MarkJelic/TEC-1G/TEC-Deck/SoundTalker/Readme.md

# SoundTalker Audio Card

- SN76489 Sound Geberator
- SP0256A-AL2 Speech Processor
- Mix in standard TEC-1 Bit-Banged sounds
- Using LM3900 Op Amp
- 4 Layer board 

This is the Schematic: TEC-Deck SoundTalker Schematic

The "GroundWalker" connector is for bit-banged sound connection from the motherboard. Input is from the left pin, and the final amplified output goes to the right pin which is connected to the mini speaker on the motherboard. Without this Sound Card installed, you would just have a jumper over these two pins so that the bit-banged sound goes direct to the speaker.

This is Beta 2, using a LM3900 for pre-amp/mixer and amplifier:
TEC-Deck SoundTalker LM3900

These are are the Back (in Green) and Front (in Red) copper layers.

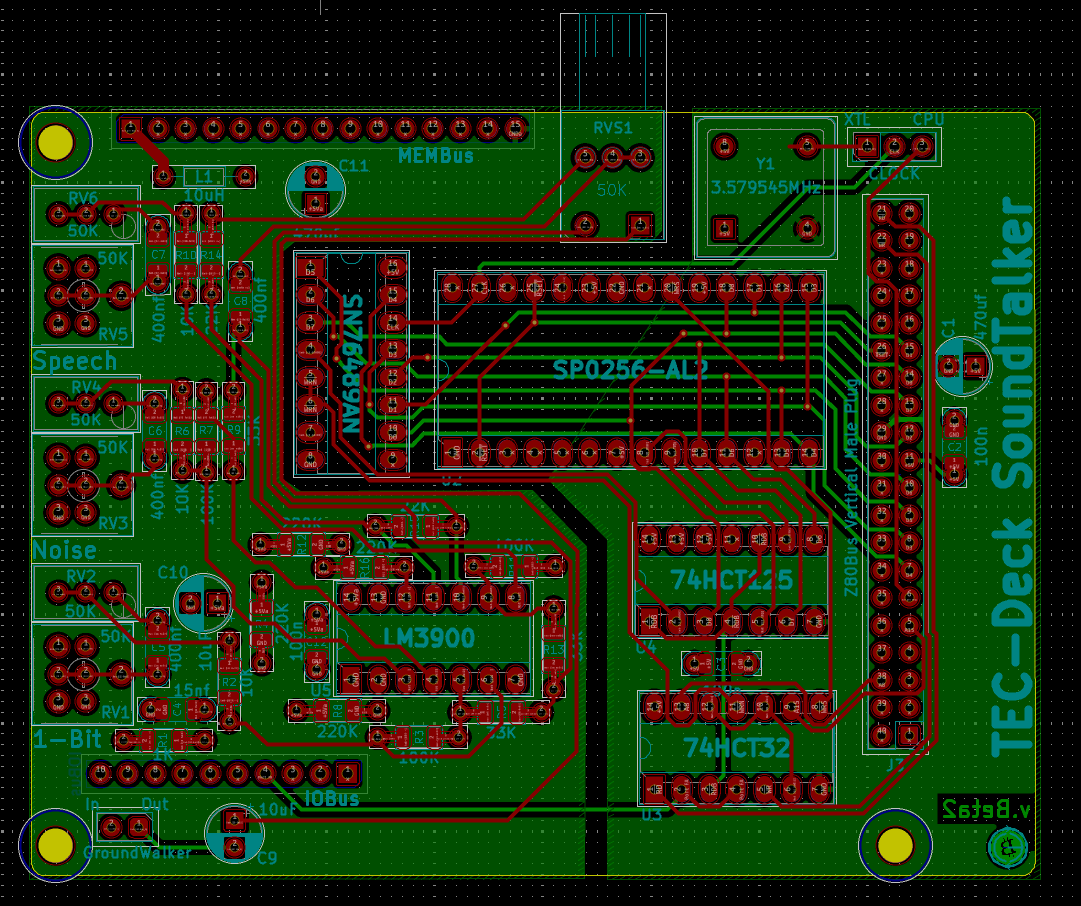
[picture p10: TEC-Deck/SoundTalker/SoundTalker-PCB_Back(G)+Front(R)_Layers.png]
TEC-Deck SoundTalker Back+Front


This is the second layer (the inner layer, closest to the back layer) and is used as the Ground plane. It also runs the source traces from each sound source, so that they are effectively shielded aby copper on all four sides.

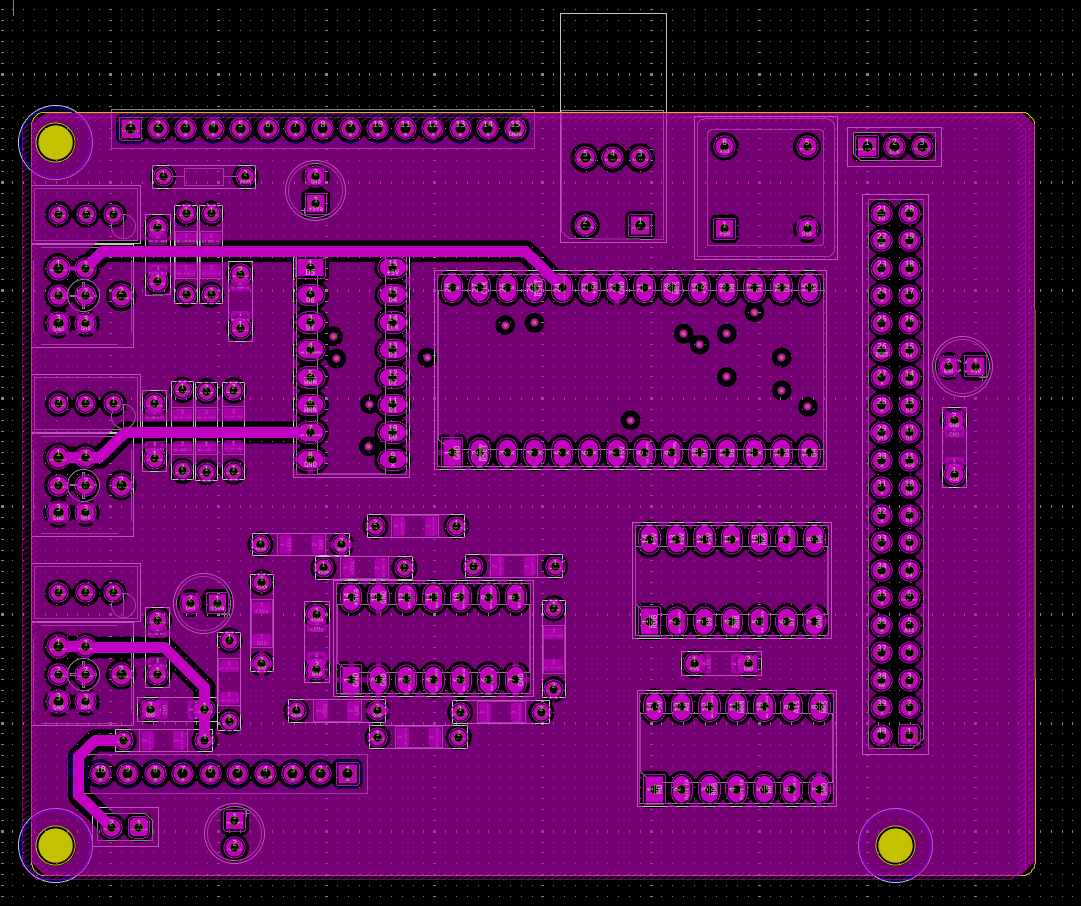
[picture p11: TEC-Deck/SoundTalker/SoundTalker-PCB_Layer2_GND-(Near_Back).png]
TEC-Deck SoundTalker Layer 2


The is the third layer (Inner layer, closer to the front of the board) and this runs the 5v plane. Note the split. Both are the same 5v source from the main motherboard, but the left hand (audio) side has an additional 10uH inductor to further smooth the 5v for the amplifier section.

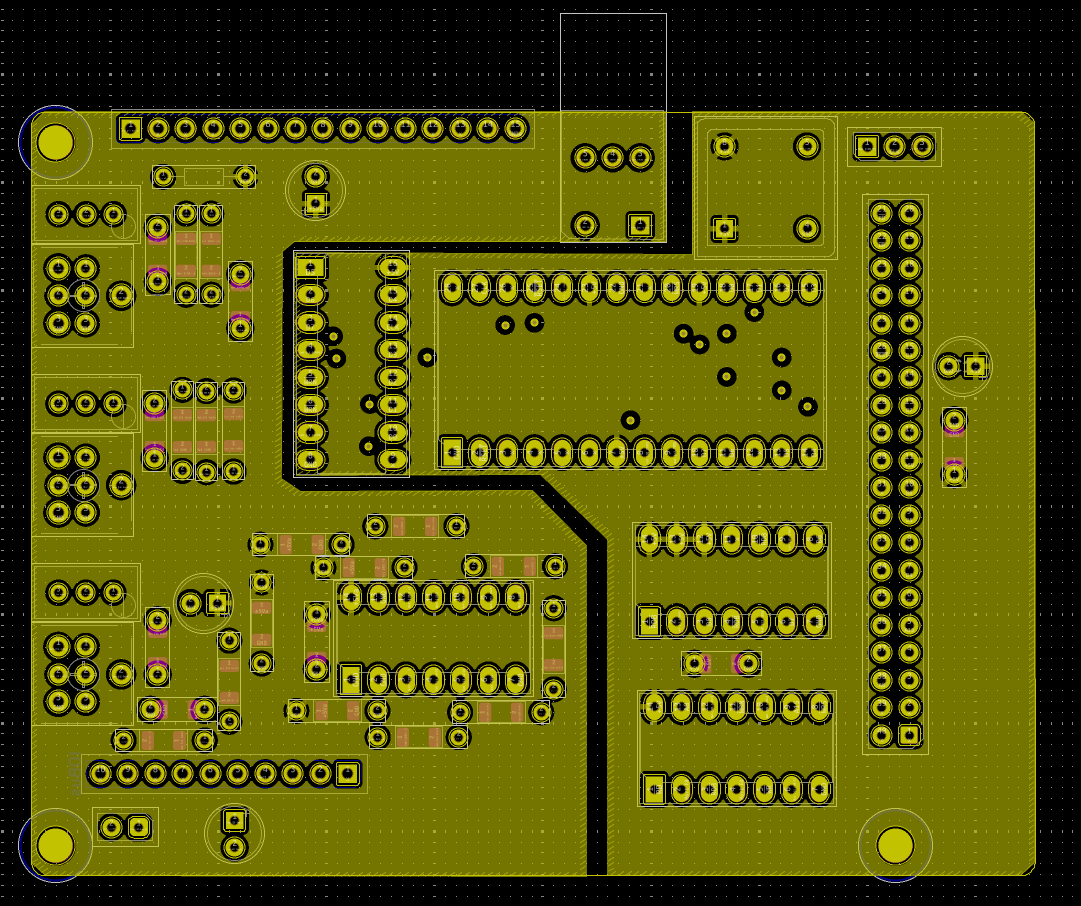
[picture p12: TEC-Deck/SoundTalker/SoundTalker-PCB_Layer3_5V-(Near_Front).png]
TEC-Deck SoundTalker Layer 3
