MarkJelic/TEC-1G/Z80Bus/TMS9918_Video-Card/README.md

# TMS9918 Video Card for the Z90Bus

All design files (KiCAD) and Gerbers.

Modelled after the 9918 video card design by J.B. Lang.
https://github.com/jblang/TMS9918A
