MarkJelic/TEC-1G/Cases/7Segs/Readme.md

## 3D Printed 7 segment display bezels for the TEC-1G
### by [Fred Nichols](https://github.com/turbo-gecko/TEC/tree/main/3D%20Printing/7%20Seg%20Bezel)

7Seg Bezel 3 Piece Lit
