MarkJelic/TEC-1G/TEC-Deck/Protoboard/Readme.md

# TEC-1G TEC-Deck Protoboard

Have an idea for the TEC-1G and want to quickly prototype it over the weekend?
Then you need one of these!

[Download the Gerbers](./TEC-1G_TEC-Deck_Protoboard_v1-0_Gerbers.zip) and get yourself a set so you're always ready for your creativity to flow.
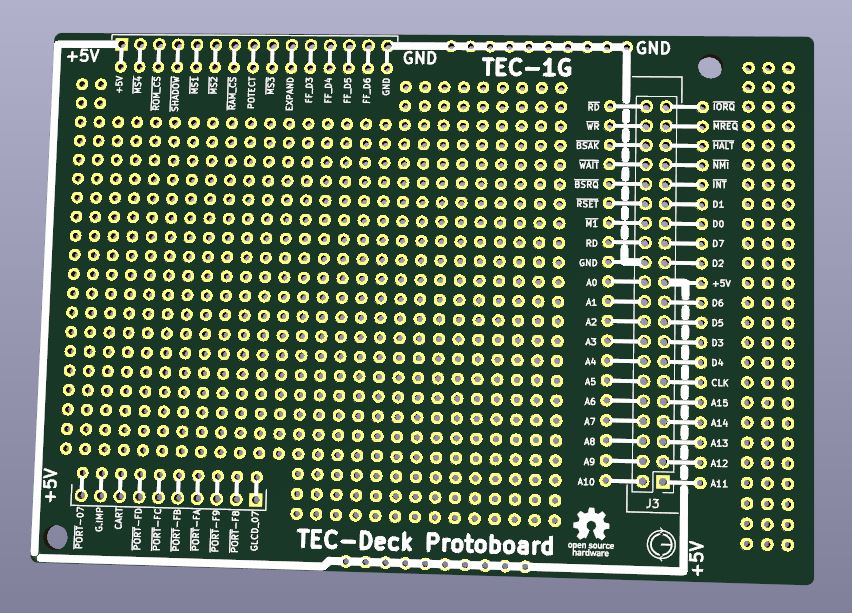
[picture p20: TEC-Deck/Protoboard/TEC-1G_TEC-Deck_ProtoBoard_v1_Render.JPG]
TEC-Deck Protoboard Render


Once you have designed your circuit and tested it out, why not make a PCB and share it with the TECian community!

[Download the KiCAD 7 design files](./TEC-1G_TEC-Deck_Protoboard_KiCAD-7.zip) of this board, and then removed the parts you don't need,
like all the through hole dots. Make sure you don't move the EdgeCuts, the Mounting Holes and of course the three headers
to ensure they line up with the TEC-1G motherboard.

If you wish to purchase a TEC-1G Proto-Pack which has this and any other Protoboards developed for the TEC-1G,
please check the listing on eBay:  https://www.ebay.com.au/itm/176243631024
