MarkJelic/TEC-1G/Cases/Retex/Readme.md

# The Original Retex Case for the TEC-1
A classic and still available after 40 years of production!

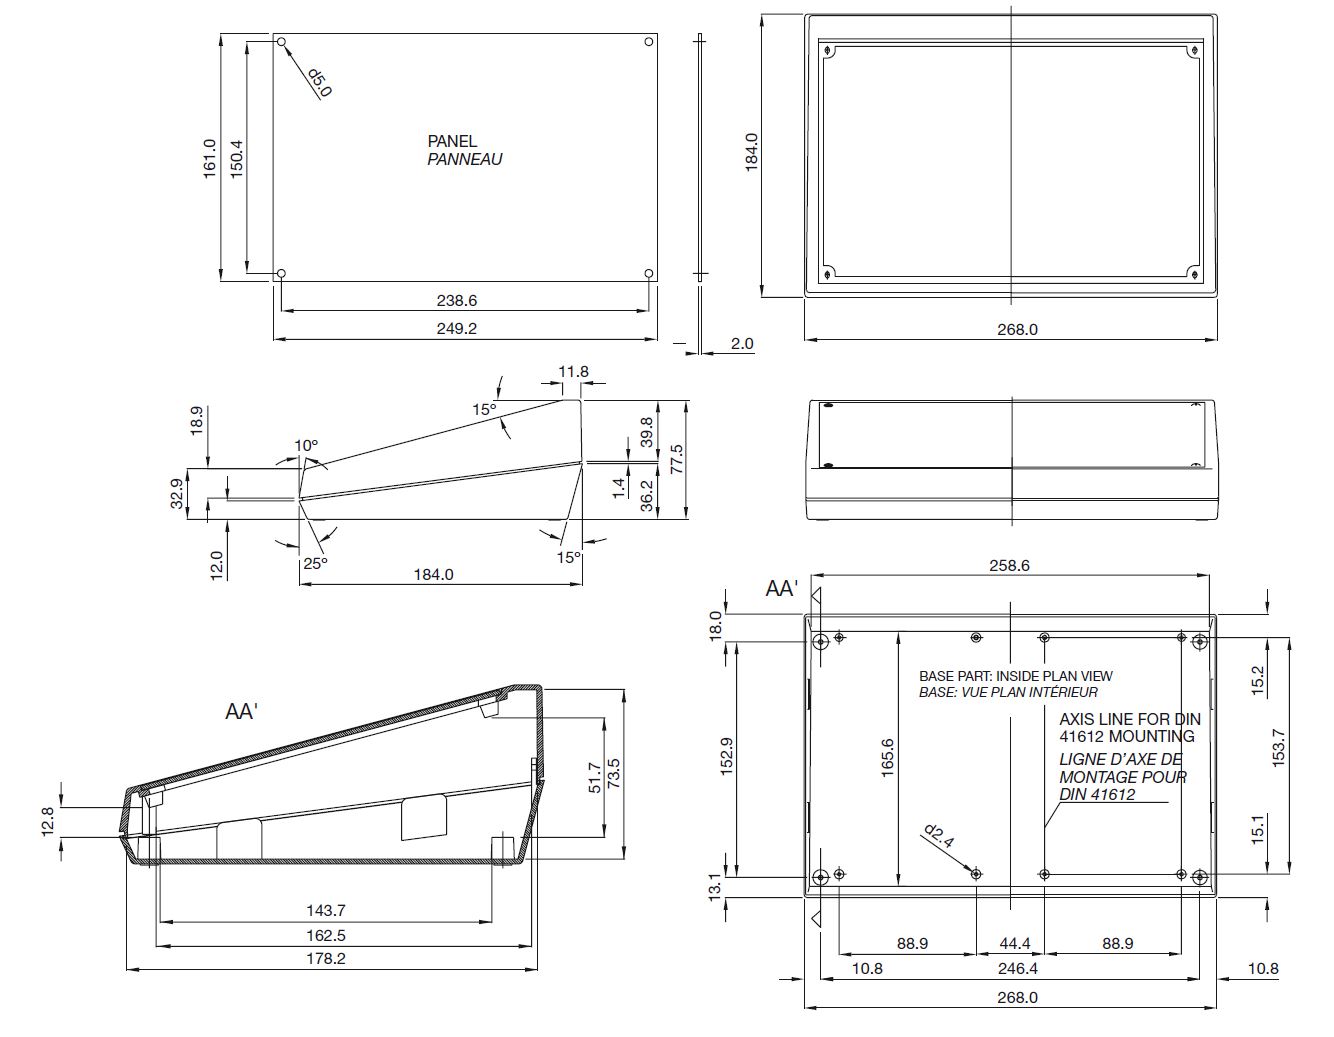
[picture p21: Cases/Retex/Retex_Case.jpg]
Retex
