MarkJelic/TEC-1G/Z80Bus/X4/Readme.md

# Z80Bus X4 System Board

Render

Here is a picture of the PCB that can be sourced from PCBWay or buy the entire kit off eBay.
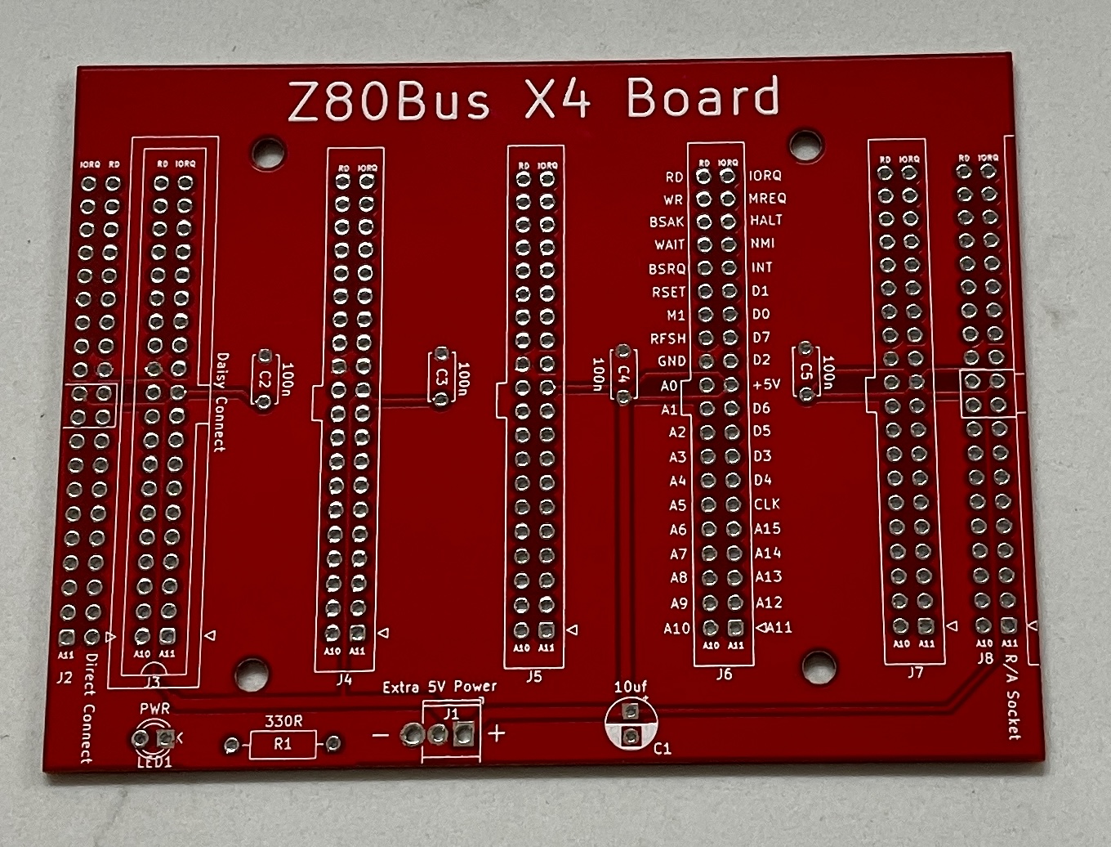
[picture p32: Z80Bus/X4/Z80Bus_X4_PCB.jpg]
PCB


Not there is much to gain from the schematic, but [here it is](Z80Bus_X4_Board_Schematic.pdf).
