MarkJelic/TEC-1G/Software/Games/8x8_LED/readme.md

# 8x8 LED Games & Demos

The original 8x8 was made with some clever soldering of 64 single colour LEDs.
Not many games were made for it but those that were, were greatly appreciated.
40 years later and the 8x8 has had a colour upgrade to full RGB which makes for
much more visually pleasing and distinguishable games and demos. 

The old mono games have been modified slightly for better keyboard layout 
and to allow hexpad / matrix keyboard input, or joystick input.
- All games default to Keyboard input.
- To activate Joystick input, hit Fn-J at the game's start menu.
- If you have the RTC card, and you turn on Joystick input, that selection will be remembered betwen games.
- To turn Keyboard input back on, hit Fn-K.

## Upcoming Titles
- Killer Tomatoes
- Maze Runner
- Minesweeper
- Scrambler
- King Tut's Snake
- RGB Invaders 3

## Pacmo  (John Hardy)

## Tecmo  (John Hardy)

## TEC Invaders 2  (Brian Chiha)

## Maze Treasure Hunt  (Brian Chiha)

## Maze  (Cameron Sheppard)

## TEC Invaders  (Cameron Sheppard)
