MarkJelic/TEC-1G/Z80Bus/TMS9918_Video-Card/KiCAD/README.md

## KiCAD Design Files

The design is NOT quite finished. I have 3 traces to complete. When this is done, will release Gerbers so people can print their own boards.

Note that I (think) I have hardwired the Port Address to be something in the range that the Colecovision and SG-1000 which gives us a HUGE library of games to port if anyone cares to.

NONE of this has been tested! You are on your own, but of course the community would love to see it come to life and be able to run some ported games! Keep us in the loop. Happy to work together.
