MarkJelic/TEC-1G/ROMs/MON3/readme.md

# Mon 3 User Guide

Mon3 (Talking Electronics Computer Monitor version 3) is custom-built for
the TEC-1G Single Board Z80 Computer. Mon3 is the heart of the TEC-1G. It
brings the hardware to life. Consider it an Operating System that provides
the ability to program the TEC. The monitor is jam-packed with features,
designed for beginners who are just learning to code Z80 and rich enough
for the advanced software developer.

A comprehensive User Guide has been provided that details how to use MON3.
Please download the **MON3 User Guide** linked in the File Links, below.

## File Links
| File | Description | Version |
|---|---|---|
| [MON3 for TEC-1G](./MON3-1G_BC25-16.bin) | Download and burn to a 16k ROM | 1.6 |
| [MON3 Change Log](./release_notes.md) | MON3 Change Log and Release Notes | 1.6 |
| [MON3 User Guide](./MON3_User_Guide_v1.6.pdf) | MON3 User Guide in PDF format | 1.6 |
| [MON3 API Guide](./api.md) | A summary of the APIs available in MON3 | 1.5 |

## A Brief Functional Description
The User Guide is a great resource that we recommend you print off and have at hand when writing
any programs for the TEC-1G.  Below are a few "Quick Reference" points that could also help.

###  Function Keys
Many of the function keys are just shortcuts to some of the Main Menu items,
like starting an Intel HEX Load. But others are really handy functions that can help
when programming "on the metal" of the TEC-1G. Here is a list of what the functions do.

Remember, to activate any of these, **Press and Hold the Fn Key down** while pressing on the corresponding function number.
Only release the Fn Key after the function starts. (There is a bit of a delay as to when the Cold Reset recognises you still pressing the Fn Key down, otherwise it just does a Warm Reset.)

| Key | Description | Implemented |
|---|---|---|
| Fn-RESET | Cold Boot the TEC-1G as if you just turned the Power On | 1.0 |
| Fn-AD (ESC) | Main Menu | 1.0 |
| Fn-GO (Enter) | Help Menu for Shortcut Fn- Keys | TBA |
| Fn-Minus (Left) | Delete current byte and SmartCopy™ RAM down | 1.0 |
| Fn-Plus (Right) | Insert a $00 byte and SmartCopy™ RAM up | 1.0 |
| Fn-0 | Configure QuickJump™ Locations | 1.3 |
| Fn-1 | QuickJump™ to Location 1 (Default is $4000. Stored in RTC) | 1.3 |
| Fn-2 | QuickJump™ to Location 2 (Stored in RTC) | 1.3 |
| Fn-3 | QuickJump™ to Location 3 (Stored in RTC) | 1.3 |
| Fn-4 | Initiate Intel HEX Load | 1.2 |
| Fn-5 | Toggle Terminal Output to GLCD. | 1.5 |
| Fn-6 | | TBA |
| Fn-7 | | TBA |
| Fn-8 | NOP Block Fill (Start, End, Value) | 1.5 |
| Fn-9 | | TBA |
| Fn-A | Restore Backup (Performs reverse of Fn-B) | 1.5 |
| Fn-B | Backup a block of memory from one location to another | 1.1 |
| Fn-C | SmartCopy™ a block of code from one location to another  | 1.0 |
| Fn-D | Disassembly View | 1.0 |
| Fn-E | Expand flag toggled (Bank 2, Pages 0 & 1)  | 1.1 |
| Fn-F | File Manager (SD Card) | 1.6 |

## Memory Map
One of the most clever things about the TEC-1G is the unique way it handles the limited 64K memory map
of the Zilog Z80.  The TEC-1G introduced 16Kb of ROM, yet was able to maintain backward compatibility with 2K ROMa,
that in the original TEC-1 was located right at the very bottom ($0000). If you want to find out more, head over to
[The Memory Map](https://github.com/MarkJelic/TEC-1G/blob/main/Documentation/memmap.md)
