MarkJelic/TEC-1G/Documentation/LCD_Cheat_Sheet.pdf

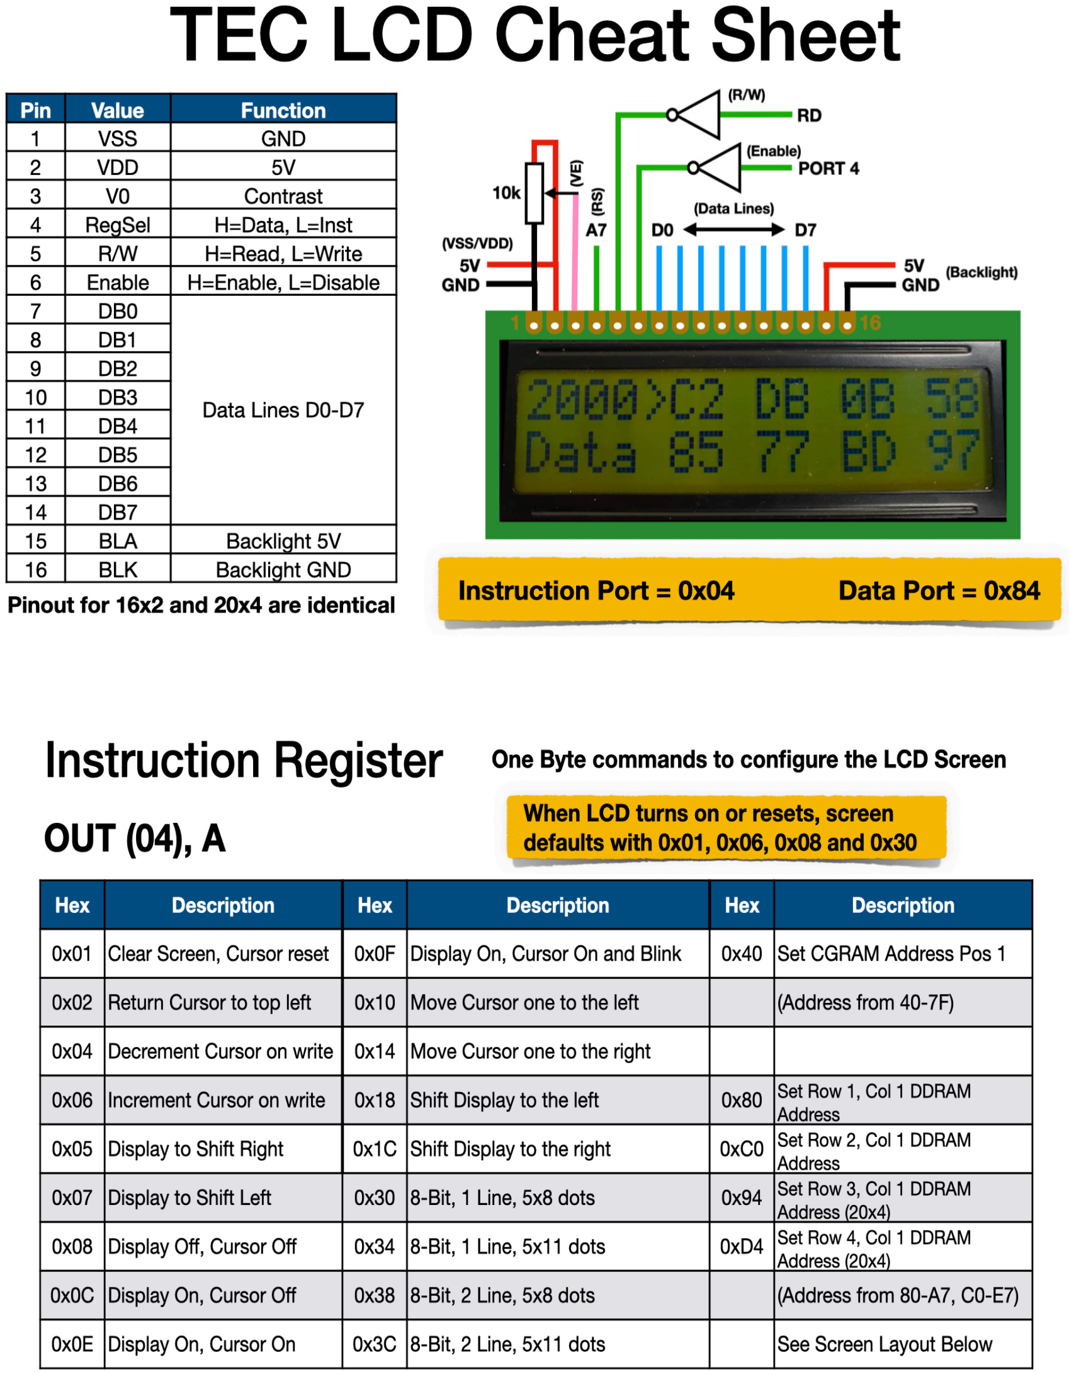
[picture p40: page 1]
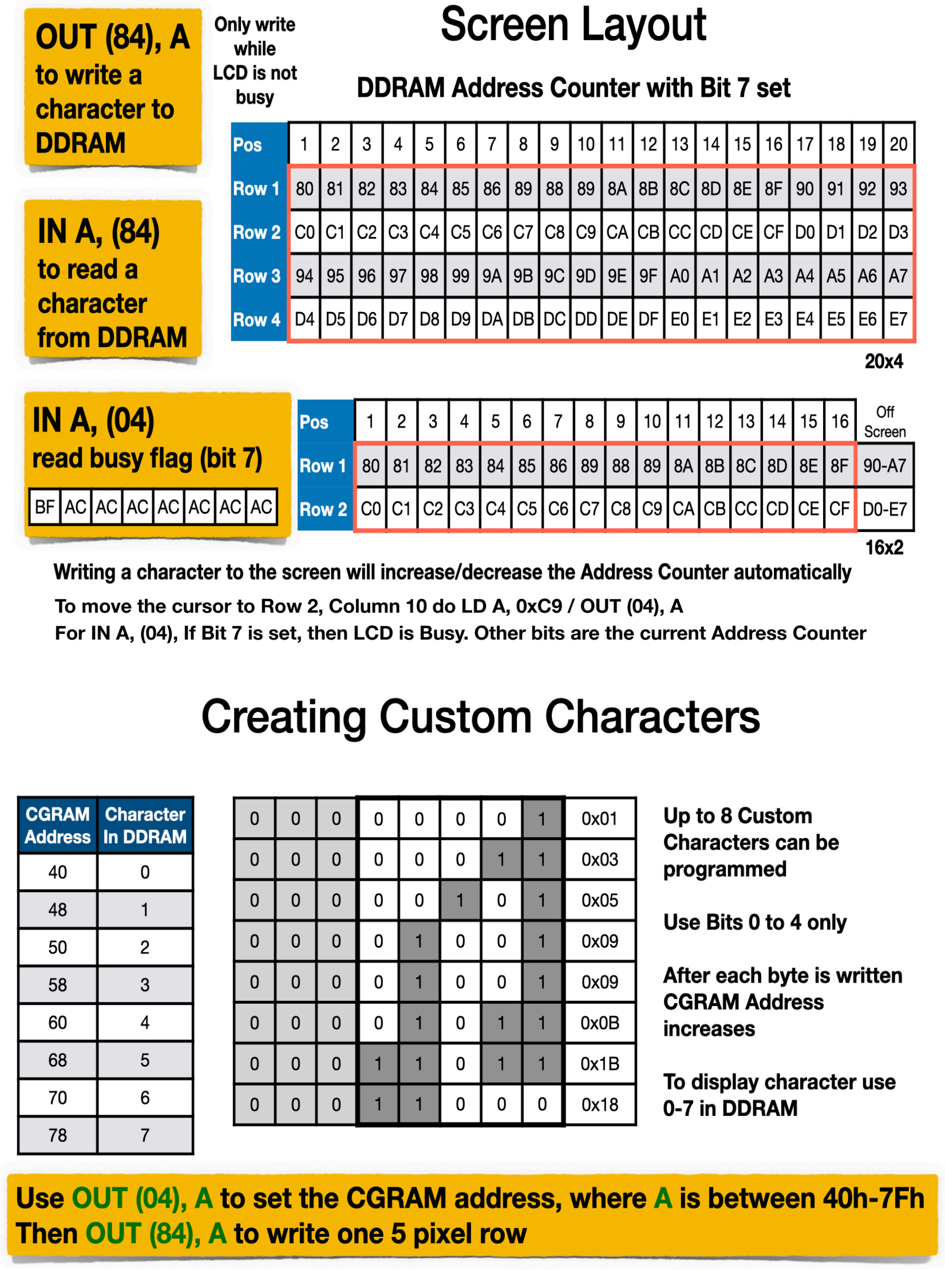
[picture p41: page 2]

## To move the cursor to Row 2, Column 10 do LD A, 0xC9 / OUT (04), A

For IN A, (04), If Bit 7 is set, then LCD is Busy. Other bits are the current Address Counter

# Character Table

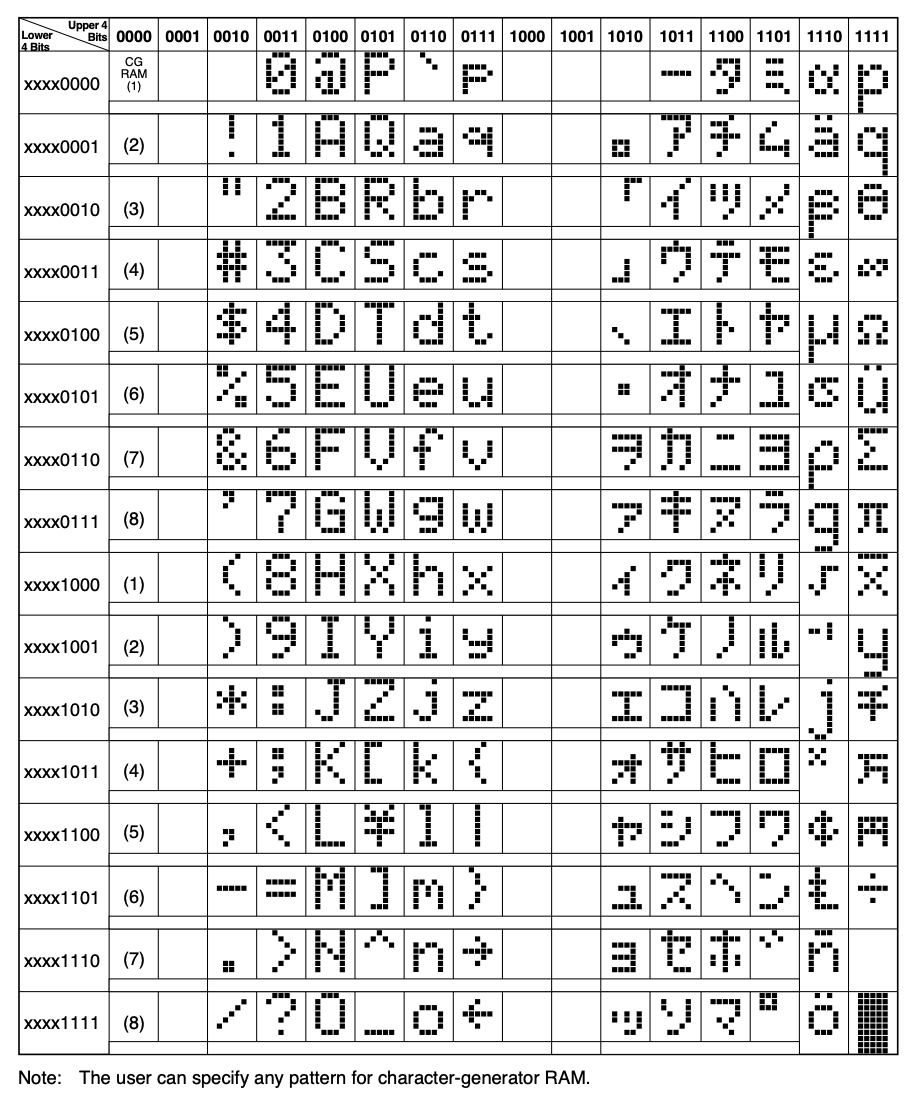
[picture p42: page 3]

# Example using CGRAM and DDRAM

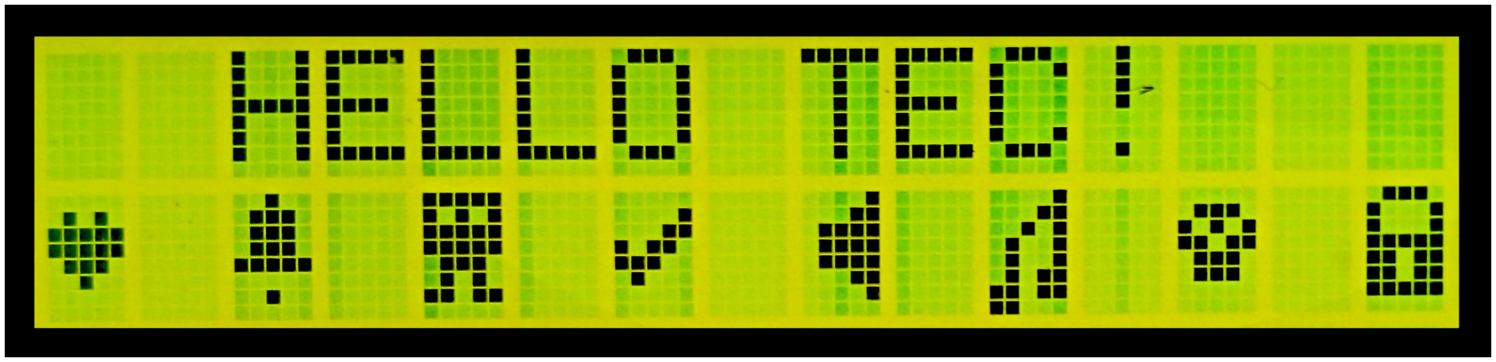
[picture p43: figure]

## Compiled by Brian Chiha v1.1

LCD_IR: | EQU | 04H ;Instruction Port
LCD_DR: | EQU | 84H ;Data Port

START:
; LCD set up
CALL | CHECK_BUSY | ;Check for LCD Busy
LD | A,0CH | ;Display On, Cursor Off
OUT | (LCD_IR),A | ;Send to Instruction Register (IR)
CALL | CHECK_BUSY | ;Check for LCD Busy
LD | A,38H | ;8-Bit, 2 Lines, 5x8 Characters
OUT | (LCD_IR),A | ;Send to Instruction Register (IR)

; Tell the LCD that next data will be to CGRAM
CALL | CHECK_BUSY | ;Check for LCD Busy
LD | A,40H | ;CGRAM entry
OUT | (LCD_IR),A | ;Send to Instruction Register (IR)

; Save multiple characters to CGRAM using lookup table and OUTI
LD | BC,4000H | LCD_DR | ;B=40 (8 letters), C=84 (port number)
LD | HL,TABLE | ;LCD custom character table
LOOP1:
CALL | CHECK_BUSY | ;Check for LCD Busy
OUTI | ;Send (HL) to port C, Decrement B, Increment HL
JR | NZ, LOOP1 | ;OUTI sets zero if B=0

; Display first line text
CALL | CHECK_BUSY | ;Check for LCD Busy
LD | A,82H | ;Move Cursor to Row 1, Col 3
OUT | (LCD_IR),A | ;Send to Instruction Register (IR)

; Send multiple characters using lookup table and OUTI
LD | BC,0A00H | LCD_DR | ;B=0A (10 letters), C=84 (port number)
LD | HL,TEXT | ;LCD text table
LOOP2:
CALL | CHECK_BUSY | ;Check for LCD Busy
OUTI | ;Send (HL) to port C, Decrement B, Increment HL
JR | NZ, LOOP2 | ;OUTI sets zero if B=0

; Display new characters
CALL | CHECK_BUSY | ;Check for LCD Busy
LD | A,0C0H | ;Move Cursor to Row 2, Col 1
OUT | (LCD_IR),A | ;Send to Instruction Register (IR)

; Send multiple characters using lookup table and OUTI
LD | BC,0800H | ;B=08 (letters), C=0 (CGRAM ref)
LOOP3:
CALL | CHECK_BUSY | ;Check for LCD Busy
LD | A,C | ;Send Custom Character
OUT | (LCD_DR),A | ;Send to Data Register (DR)
INC | C | ;Increase C to next CGRAM ref in DDRAM
CALL | CHECK_BUSY | ;Check for LCD Busy
LD | A,20H | ;Send Space Character
OUT | (LCD_DR),A | ;Send to Data Register (DR)
DJNZ | LOOP3 | ;Repeat for all 8 characters
HALT | ;Pause the CPU

TEXT:
DB "HELLO TEC!"
TABLE:
DB | 00H,0AH,1FH,1FH,0EH,04H,00H,00H | ;Heart
DB | 04H,0EH,0EH,0EH,1FH,00H,04H,00H | ;Bell
DB | 1FH,15H,1FH,1FH,0EH,0AH,1BH,00H | ;Alien
DB | 00H,01H,03H,16H,1CH,08H,00H,00H | ;Tick
DB | 01H,03H,0FH,0FH,0FH,03H,01H,00H | ;Speaker
DB | 01H,03H,05H,09H,09H,0BH,1BH,18H | ;Note
DB | 00H,0EH,15H,1BH,0EH,0EH,00H,00H | ;Skull
DB | 0EH,11H,11H,1FH,1BH,1BH,1FH,00H | ;Lock

; Routine to check the Busy Flag (Bit 7) CHECK_BUSY:
IN | A,(LCD_IR) | ;Read Busy Byte
RLCA | ;Put Bit 7 in Carry Flag
JR | C, CHECK_BUSY | ;If Carry Set then LCD is busy
RET
