MarkJelic/TEC-1G/Keyboards/Tactile/6mm_Tactile_Keyboard_Labels.pdf

R | AD | C | D | E | F
| GO | 8 | 9 | A | B
| - | 4 | 5 | 6 | 7
SH | + | 0 | 1 | 2 | 3
RESET | | | | | | | 22
| | | | | | | | | | | | | 1
AD Esc | ! 1 | @ 2 | # 3 | $ ₿ 4 | % 5 | ^ 6 | & 7 | * 8 | ( 9 | ) 0 | + = | BS
13
| TAB | Q | W | E | R | T | Y | U | I | O | P | _ - | | \
13
| CAPS | A | S | D F | G | H | J | K | L | : ; | " ' | GO Enter
13
| Shift | Z | X | C | V | B | N M | < , | > . | ? / | ↑ | Shift
13
| Ctrl | Fn | SPACE | - + ← | ↓ | →
6
| | | 59
White | 55 | Spare +1 | 60
