MarkJelic/TEC-1G/Cases/BrianC/TEC-1G Case.jpg

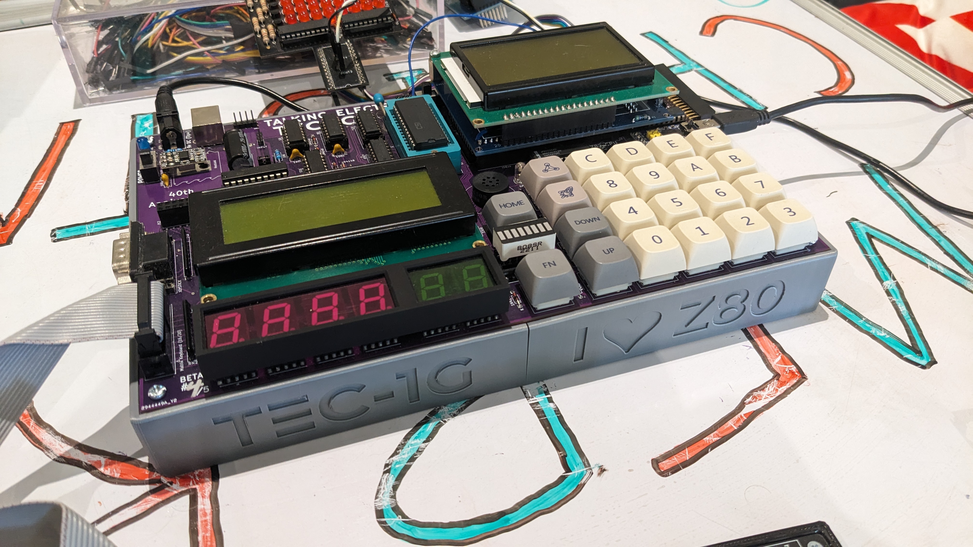
Cases/BrianC/TEC-1G Case.jpg
