MarkJelic/TEC-1G/Cases/Official/Tactile-Keyboard-Case_Purple-Front.jpg

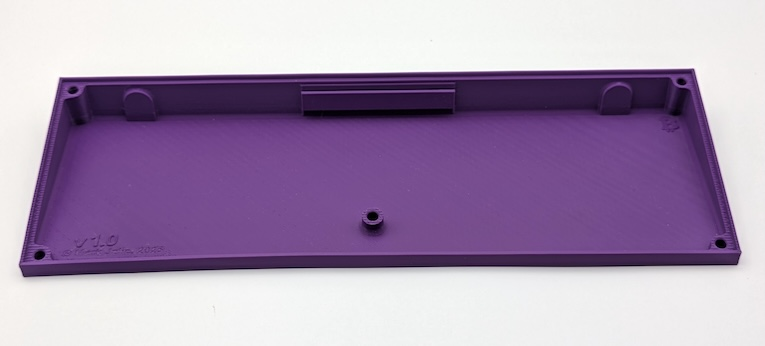
Cases/Official/Tactile-Keyboard-Case_Purple-Front.jpg
