MarkJelic/TEC-1G/Cases/Official/TEC-1G+Tactile-Keyboard_in_Cases_-_Left.jpg

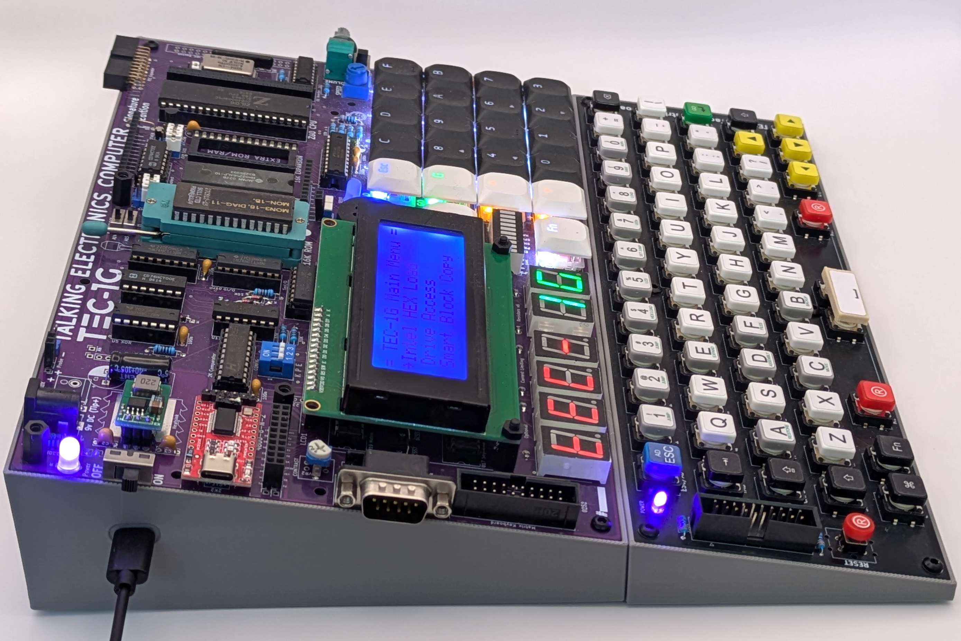
Cases/Official/TEC-1G+Tactile-Keyboard_in_Cases_-_Left.jpg
