MarkJelic/TEC-1G/Cases/Official/TEC-1G-in-Case_Back.jpg

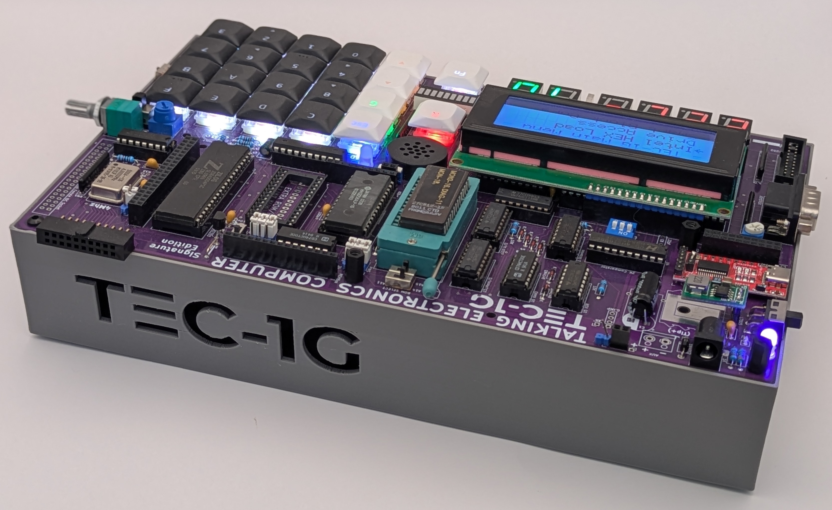
Cases/Official/TEC-1G-in-Case_Back.jpg
