MarkJelic/TEC-1G/Cases/Official/TEC-1G_Case_Tan+Grey.jpg

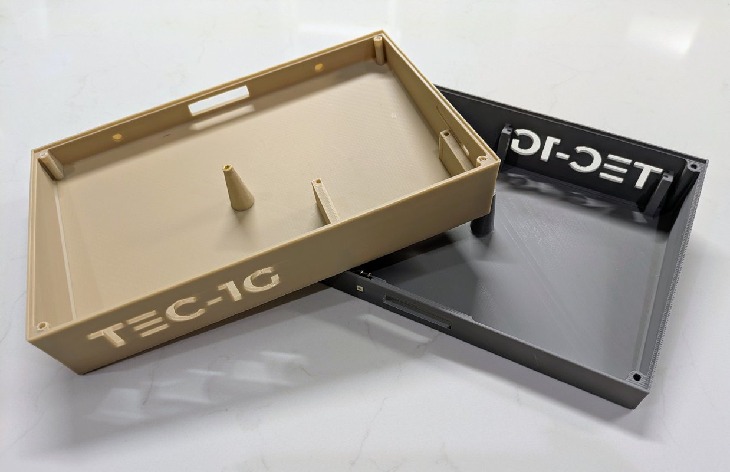
Cases/Official/TEC-1G_Case_Tan+Grey.jpg
