MarkJelic/TEC-1G/Keyboards/Mechanical/Mechncial_PCBs.jpg

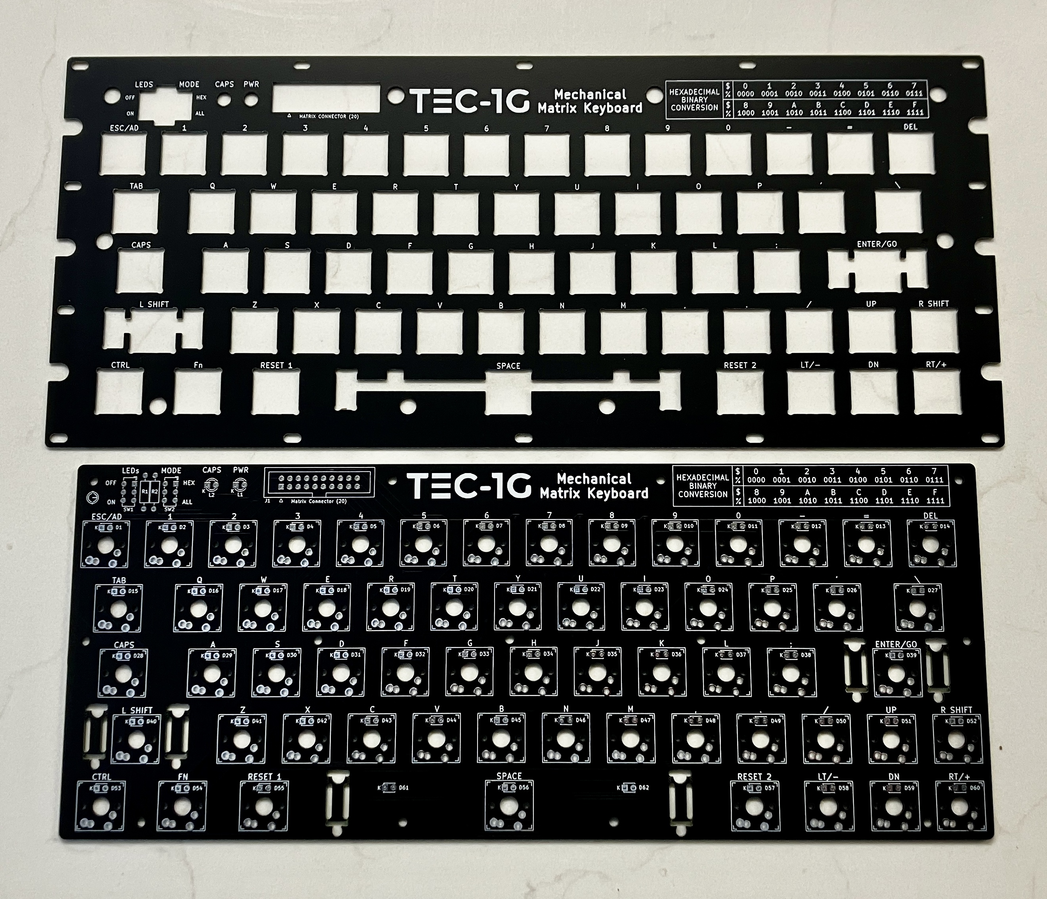
Keyboards/Mechanical/Mechncial_PCBs.jpg
