MarkJelic/TEC-1G/Keyboards/pictures/Scanning_Keyboard_Schematic1.jpg

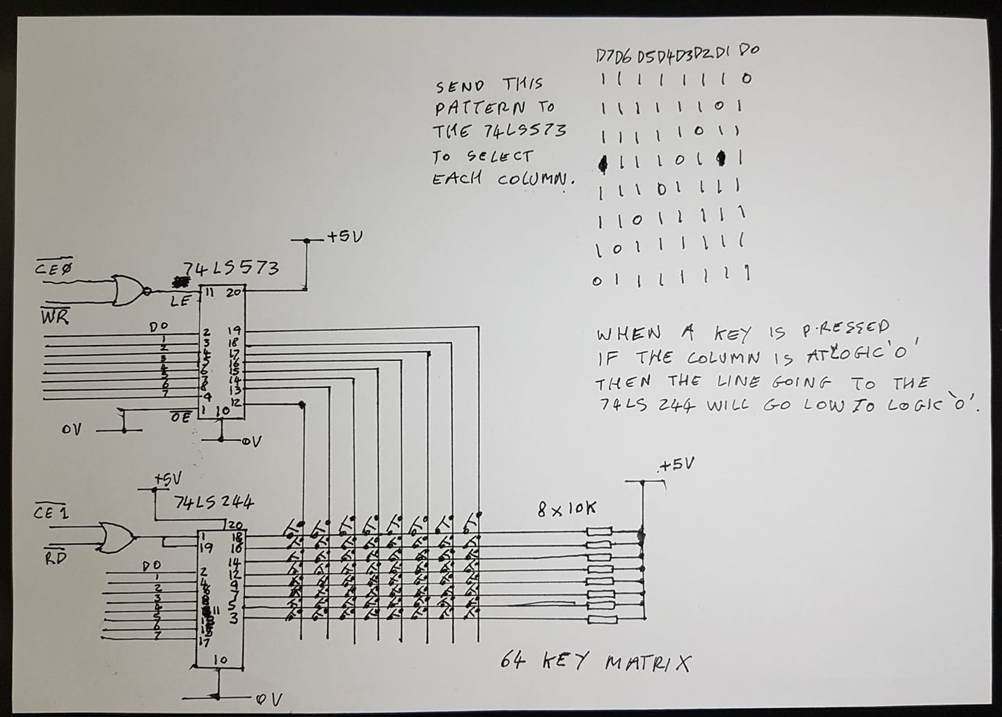
Keyboards/pictures/Scanning_Keyboard_Schematic1.jpg
