MarkJelic/TEC-1G/Keyboards/pictures/Scanning_Keyboard_Schematic2.jpg

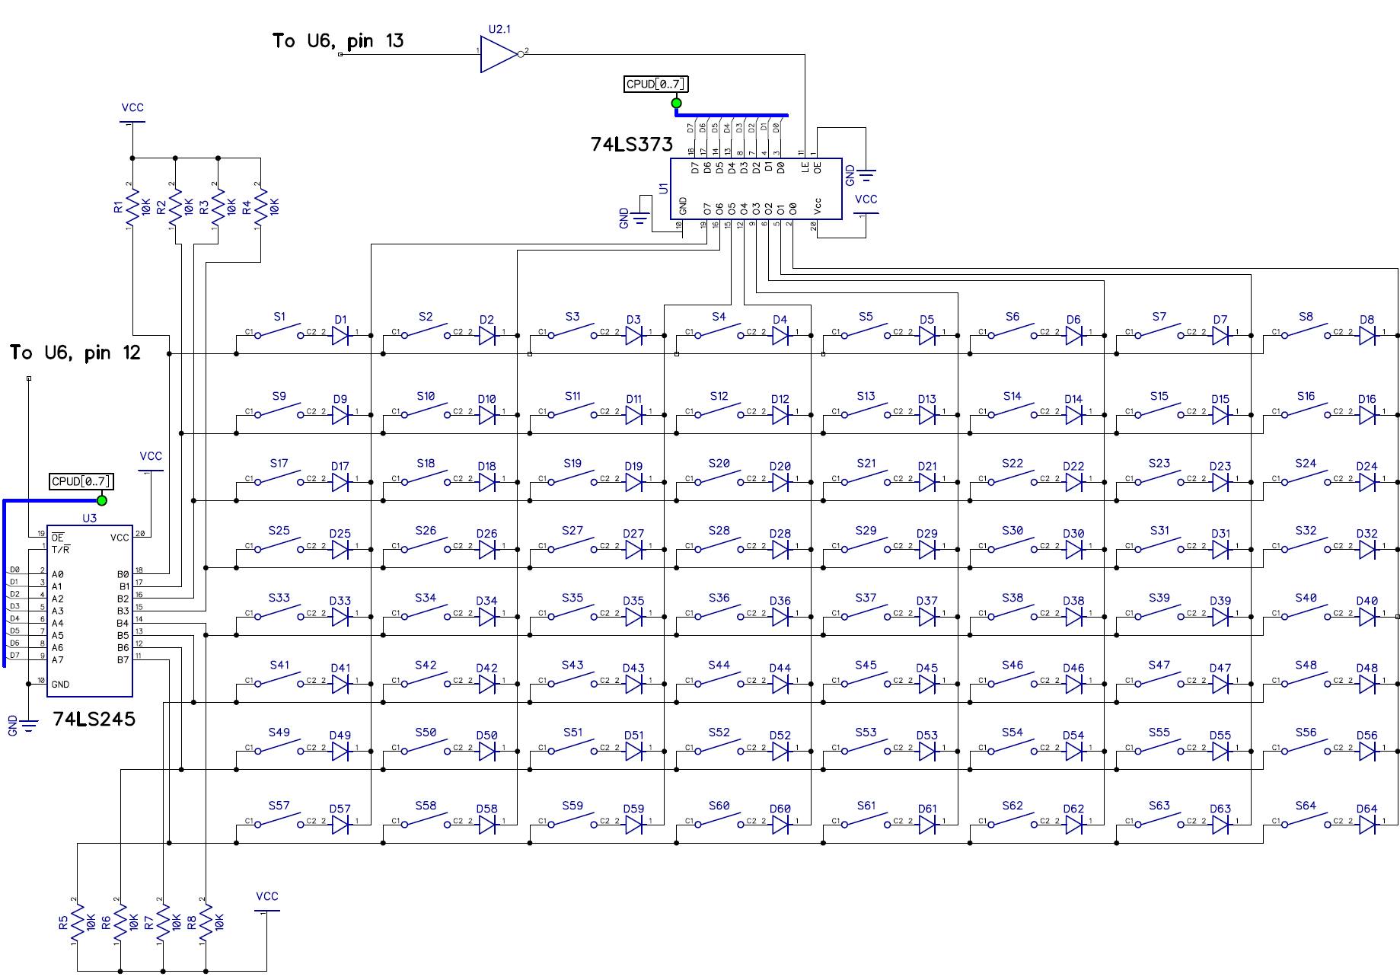
Keyboards/pictures/Scanning_Keyboard_Schematic2.jpg
