MarkJelic/TEC-1G/Keyboards/pictures/Spectrum_keyboard_for_Satellite.png

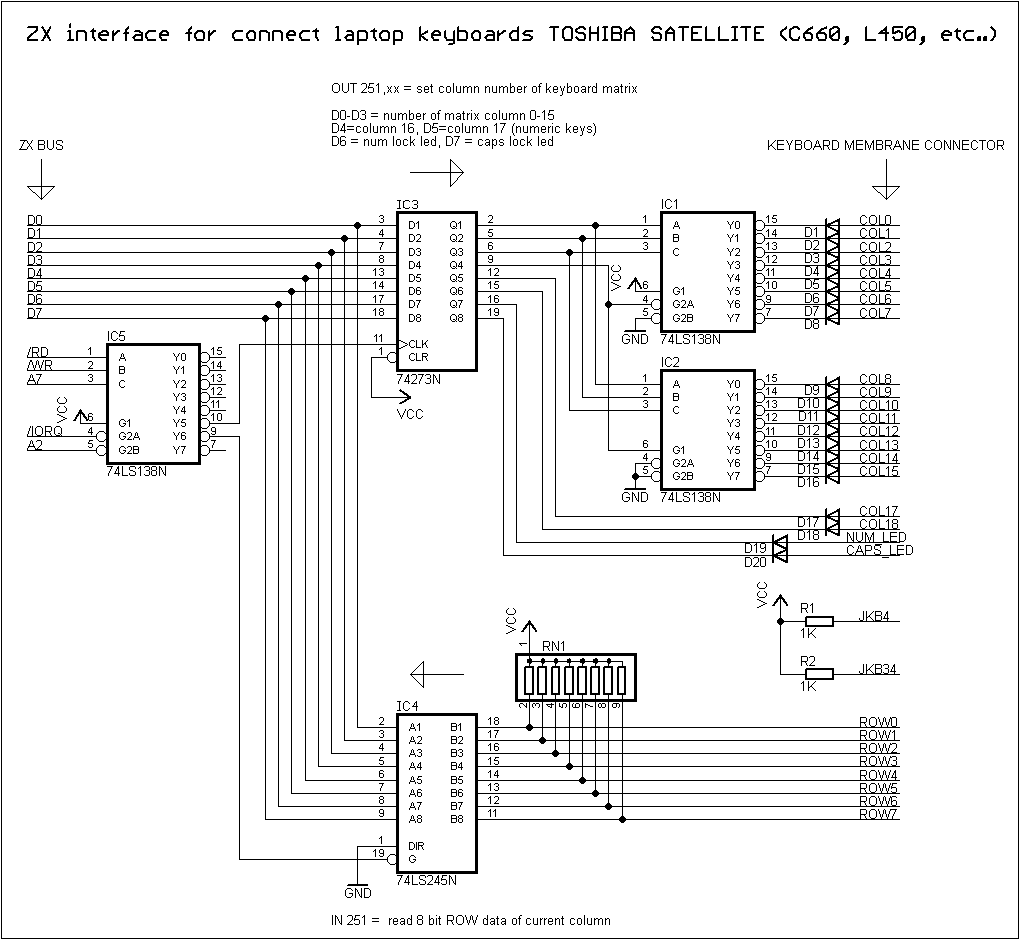
Keyboards/pictures/Spectrum_keyboard_for_Satellite.png
