MarkJelic/TEC-1G/pictures/1G Beta PCB.jpg

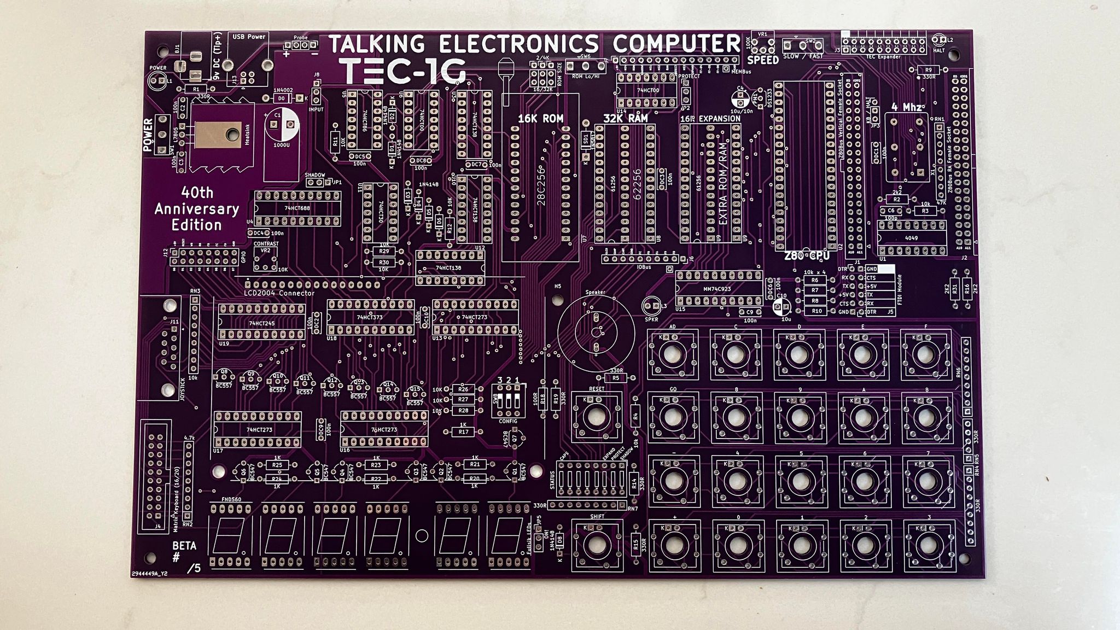
pictures/1G Beta PCB.jpg
