MarkJelic/TEC-1G/pictures/TEC-1G_Fulisik_LEDs.jpg

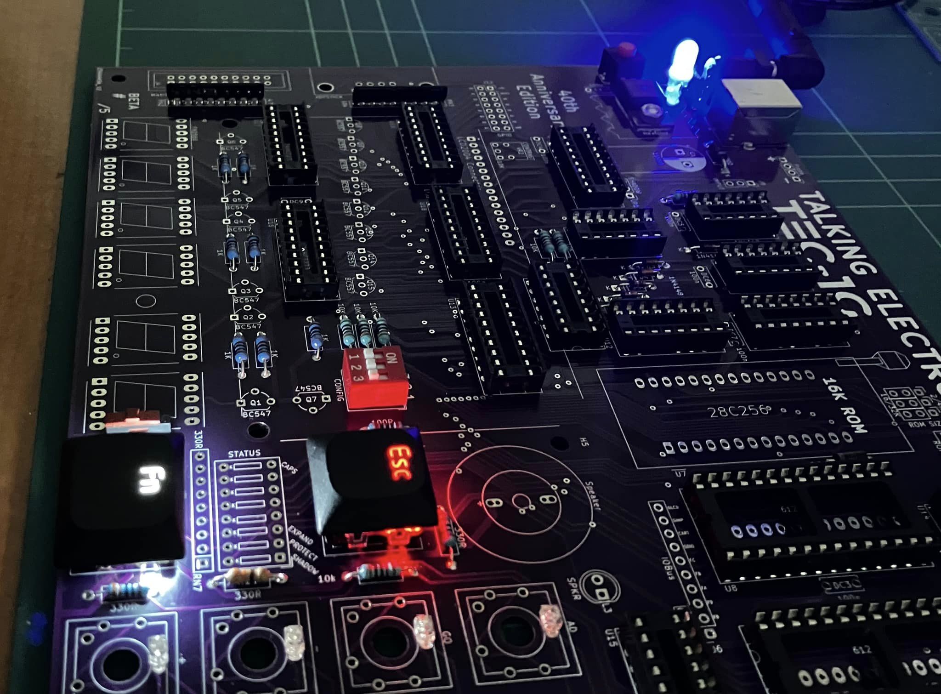
pictures/TEC-1G_Fulisik_LEDs.jpg
