MarkJelic/TEC-1G/pictures/TEC-1G_Render_Gateron_Keys.jpg

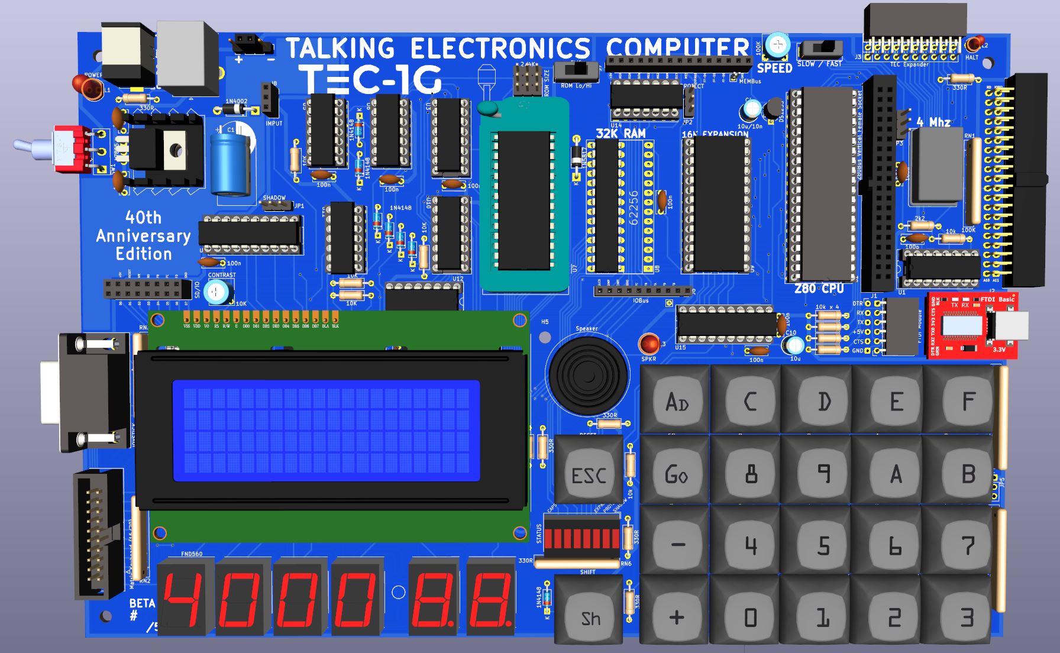
pictures/TEC-1G_Render_Gateron_Keys.jpg
