MarkJelic/TEC-1G/pictures/TEC-1G_Render_Power_Input.jpg

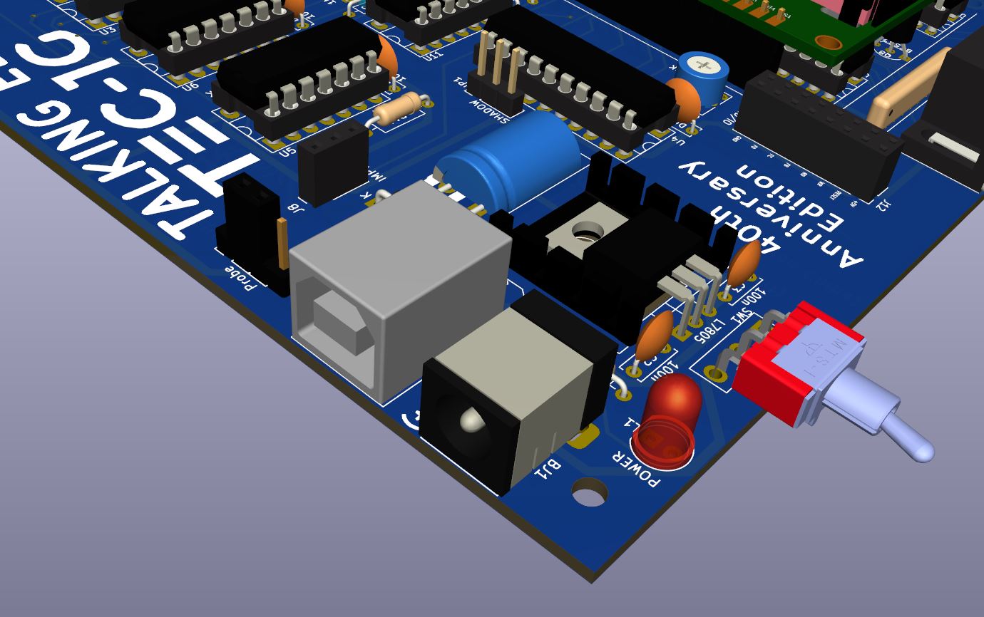
pictures/TEC-1G_Render_Power_Input.jpg
