MarkJelic/TEC-1G/pictures/TEC-1G_Render_Signatures.jpg

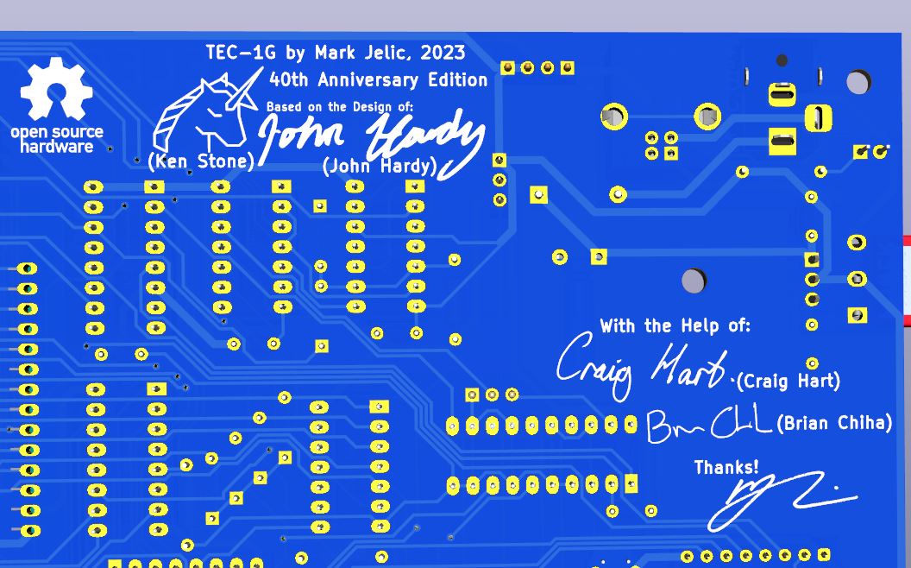
pictures/TEC-1G_Render_Signatures.jpg
