MarkJelic/TEC-1G/pictures/TEC-1G_Render_TEC_Deck.png

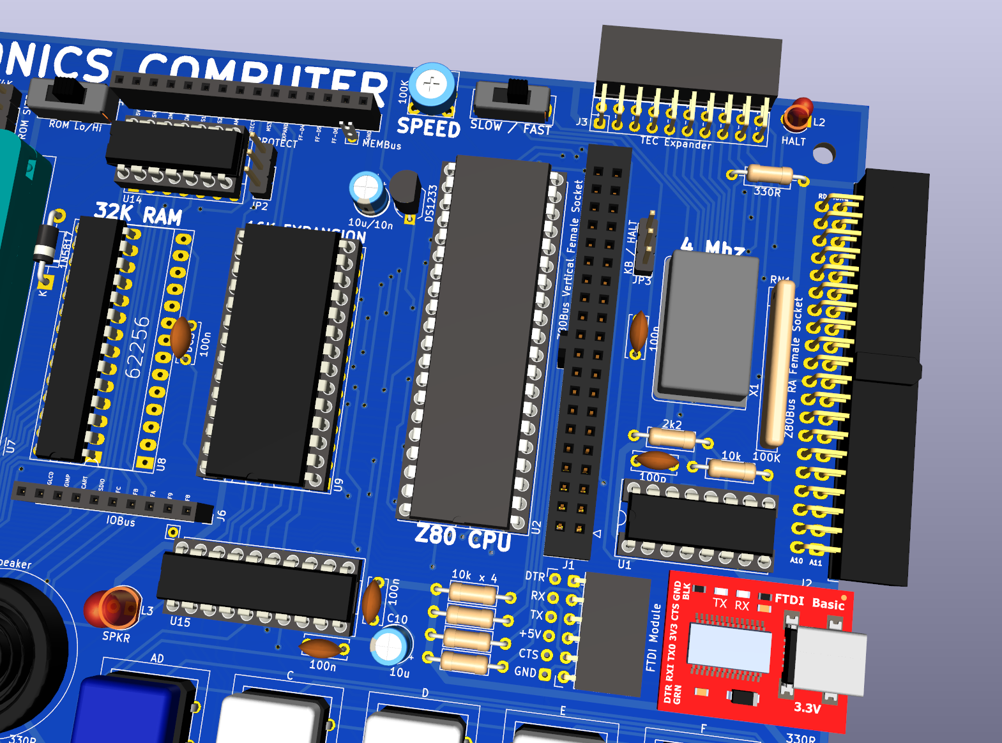
pictures/TEC-1G_Render_TEC_Deck.png
