MarkJelic/TEC-1G/TEC-Deck/_Template/TEC-Deck_Template.JPG

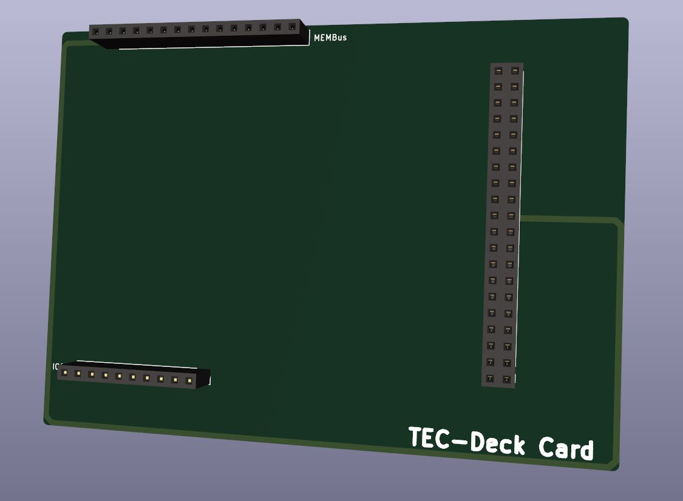
TEC-Deck/_Template/TEC-Deck_Template.JPG
