MarkJelic/TEC-1G/TEC-Deck/Graphical_LCD/LCD_connection.png

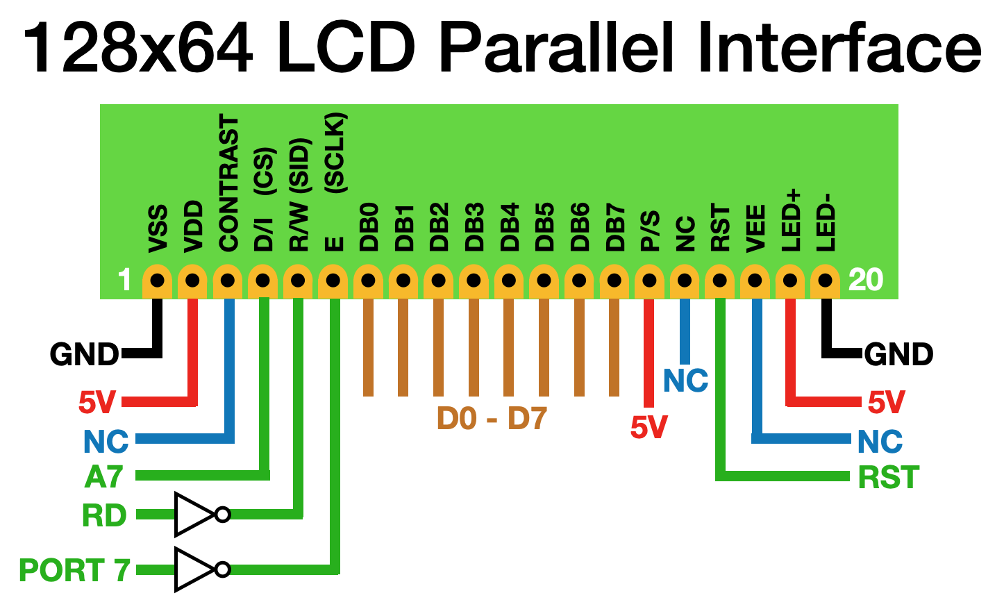
TEC-Deck/Graphical_LCD/LCD_connection.png
