MarkJelic/TEC-1G/TEC-Deck/Graphical_LCD/TEC-1G_GLCD_Kit.jpg

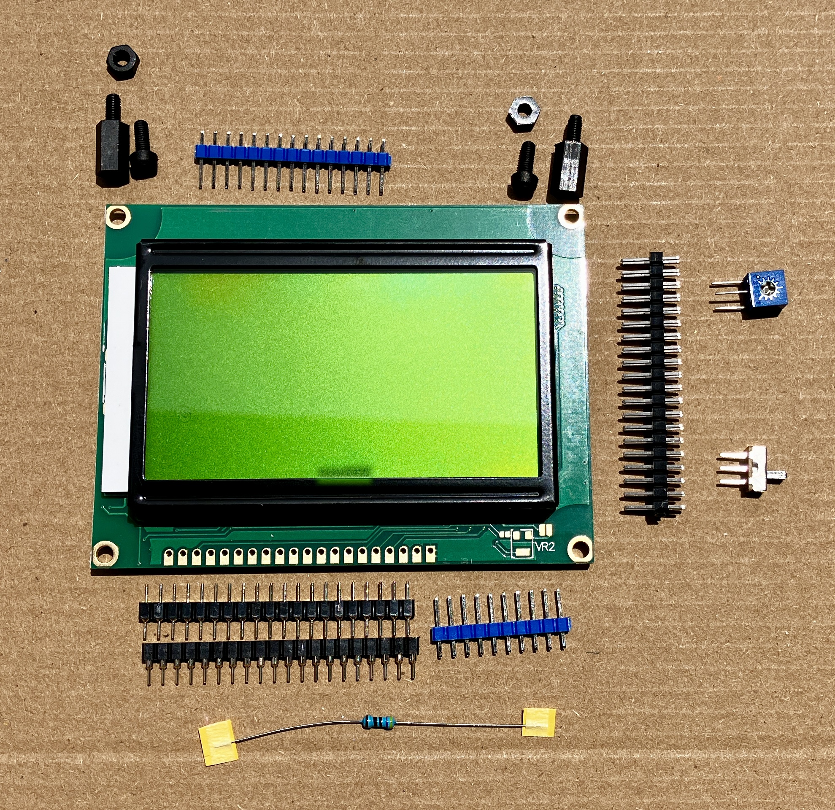
TEC-Deck/Graphical_LCD/TEC-1G_GLCD_Kit.jpg
