MarkJelic/TEC-1G/TEC-Deck/SoundTalker/SoundTalker-PCB_Back(G) and Front(R) Layers.png

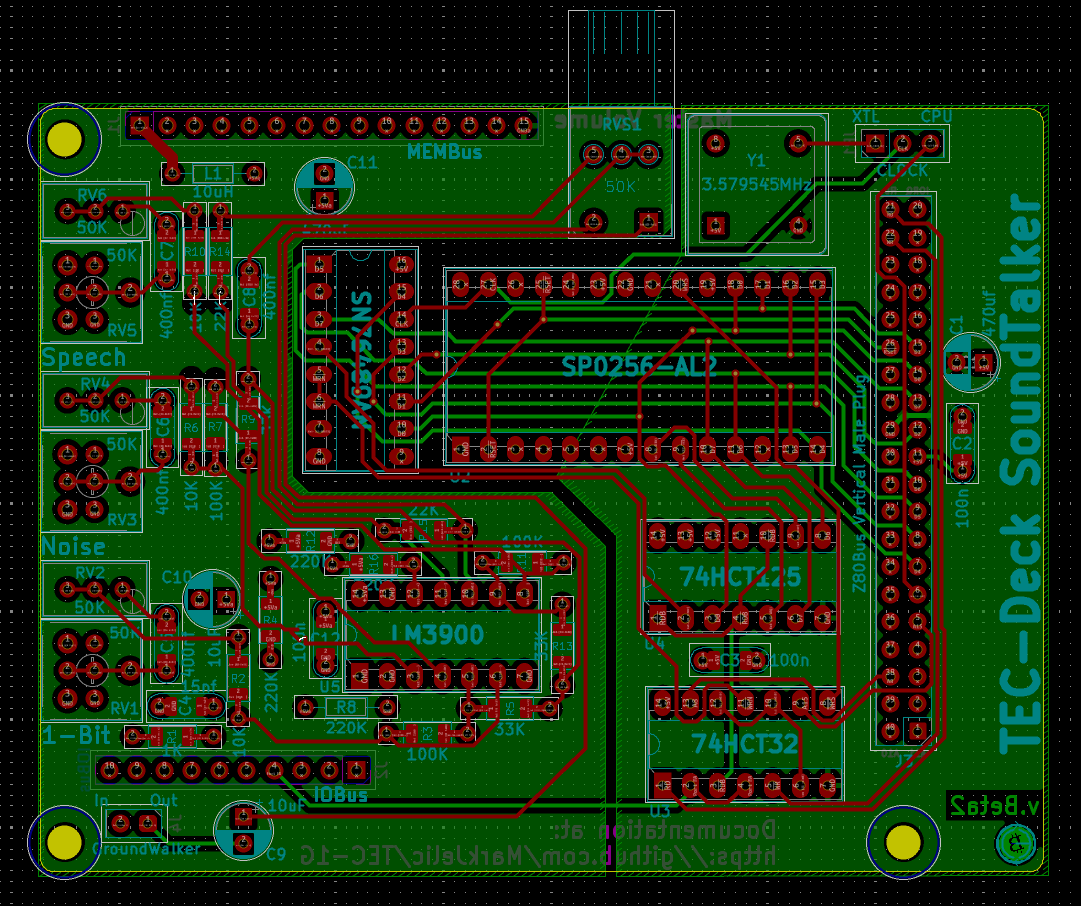
TEC-Deck/SoundTalker/SoundTalker-PCB_Back(G) and Front(R) Layers.png
