MarkJelic/TEC-1G/TEC-Deck/TMS9918_Video/Cuts-&-Bodges_v1-1.jpg

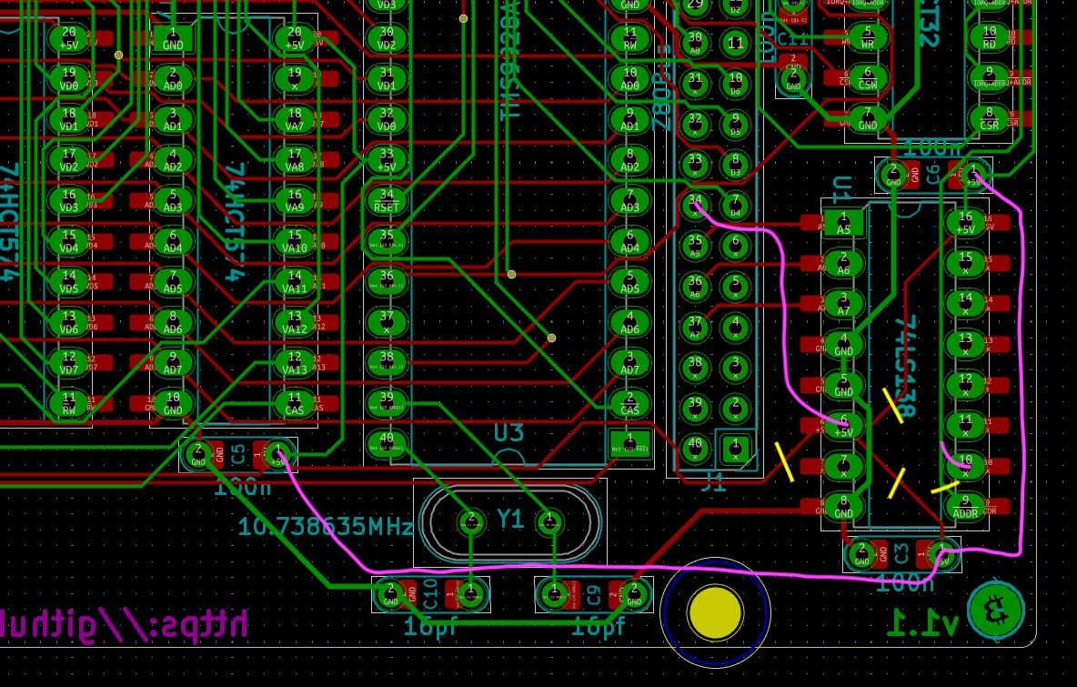
TEC-Deck/TMS9918_Video/Cuts-&-Bodges_v1-1.jpg
