MarkJelic/TEC-1G/GPIO/Printer/Readme.md

# GPIO Parallel Printer Port
| File | Description | Version |
|---|---|---|
| [Schematic](TEC-1G_GPIO_Printer_Schematic_v1-1.pdf) | It's a simple circuit, but it's honest printing. | 1.1 |
| [Parts List](./Partslist.md) | What you need to buy (and comes in the Kit) | 1.0 |
| [Assembly Instructions](./Assembly.md) | Coming Soon... | 1.0 |
| [PCB Gerbers]() | Coming Soon... | 1.0 |
| [Sample Programs](./Programs/) | Coming Soon... | 1.0 |

## What Does it Do?
It lets you connect to a parallel printer and print things!<br>
It also doubles as another general Input / Output board, much like the GPIO SD Card board.

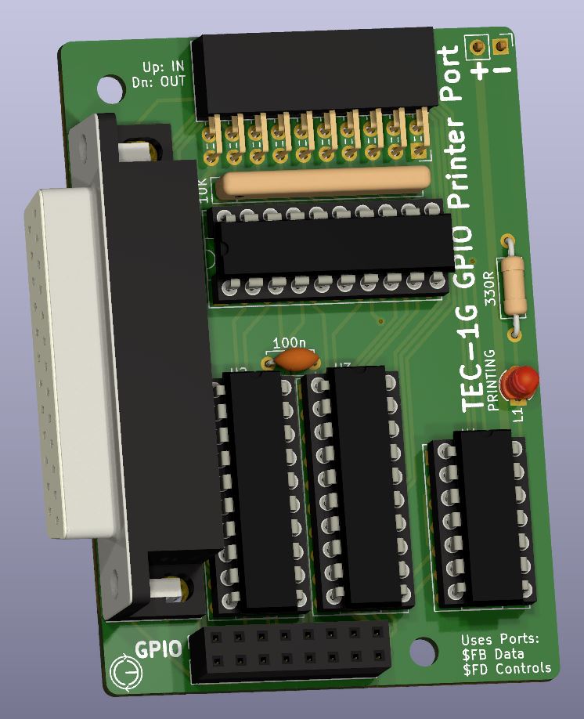
[picture p79: GPIO/Printer/pictures/TEC-1G_GPIO_Printer-Render.jpg]
TEC-1G GPIO Printer
