MarkJelic/TEC-1G/GPIO/Printer/Programs/Readme.md

# Printer Port Programs

Coming Soon®...
