MarkJelic/TEC-1G/Documentation/Assembly/pictures/capacitor_101.jpg

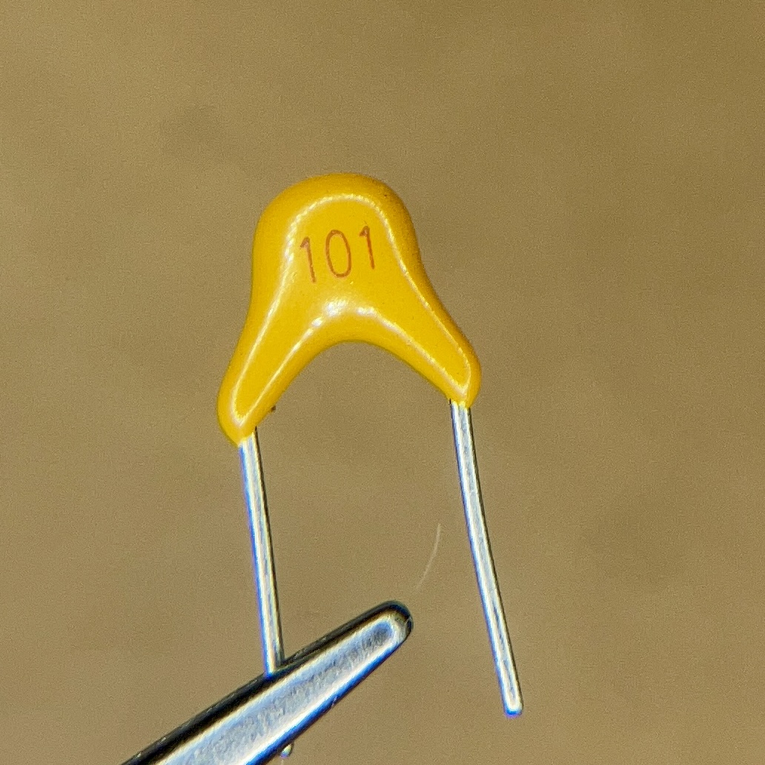
Documentation/Assembly/pictures/capacitor_101.jpg
