MarkJelic/TEC-1G/Documentation/Assembly/pictures/capacitor_103.jpg

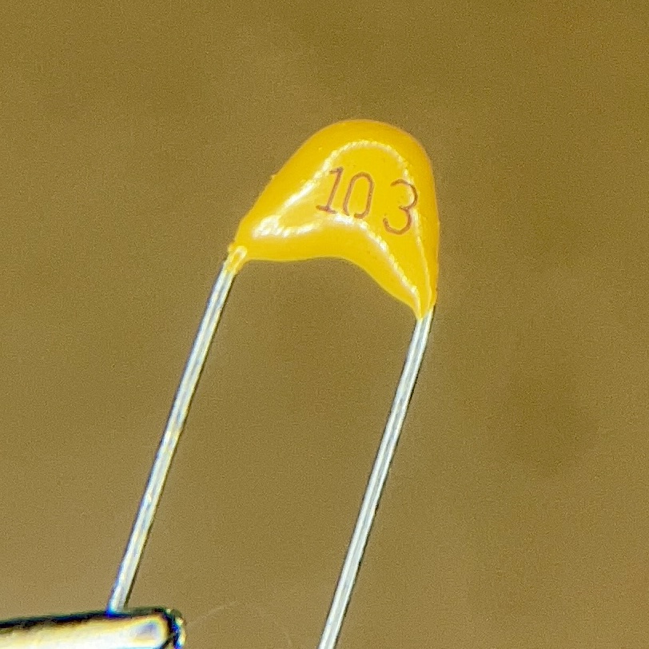
Documentation/Assembly/pictures/capacitor_103.jpg
