MarkJelic/TEC-1G/Documentation/Assembly/pictures/diode_1n.jpg

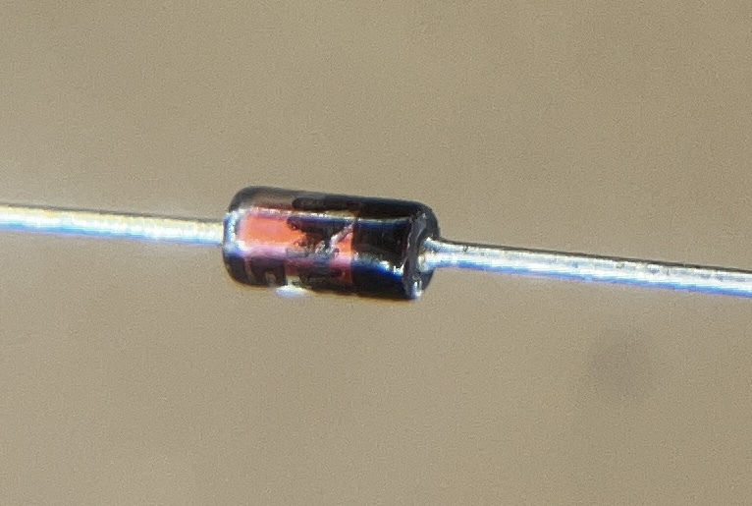
Documentation/Assembly/pictures/diode_1n.jpg
