MarkJelic/TEC-1G/Documentation/Assembly/pictures/jumper_shunted.jpg

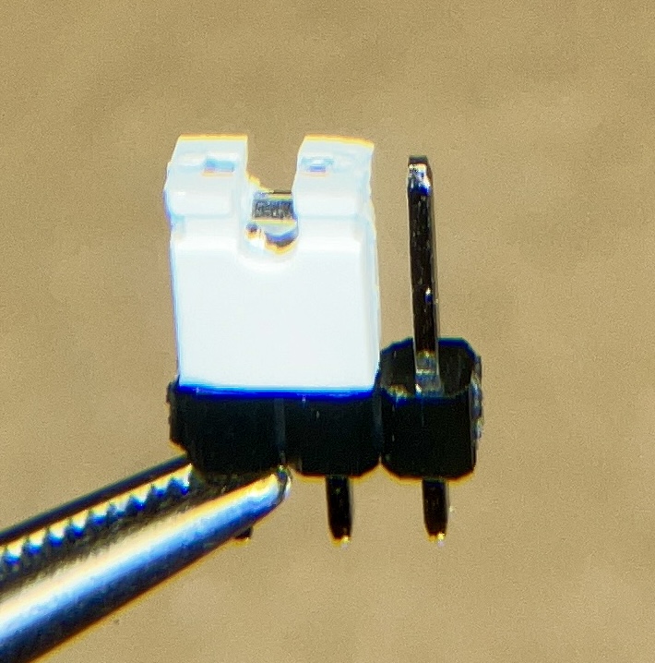
Documentation/Assembly/pictures/jumper_shunted.jpg
