MarkJelic/TEC-1G/Documentation/Assembly/pictures/power_supply.jpg

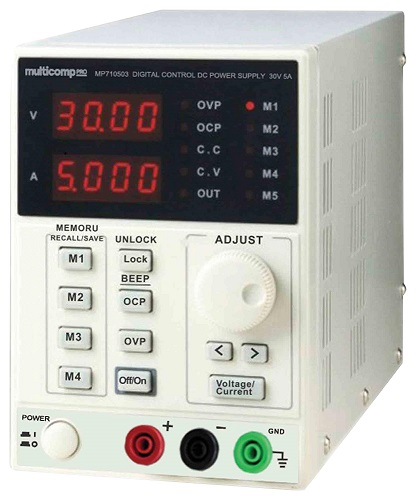
Documentation/Assembly/pictures/power_supply.jpg
