MarkJelic/TEC-1G/Documentation/Assembly/pictures/resistor-n_472.jpg

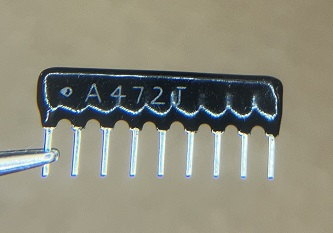
Documentation/Assembly/pictures/resistor-n_472.jpg
