MarkJelic/TEC-1G/Z80Bus/TMS9918_Video-Card/TMS9918_Video-Card.pdf

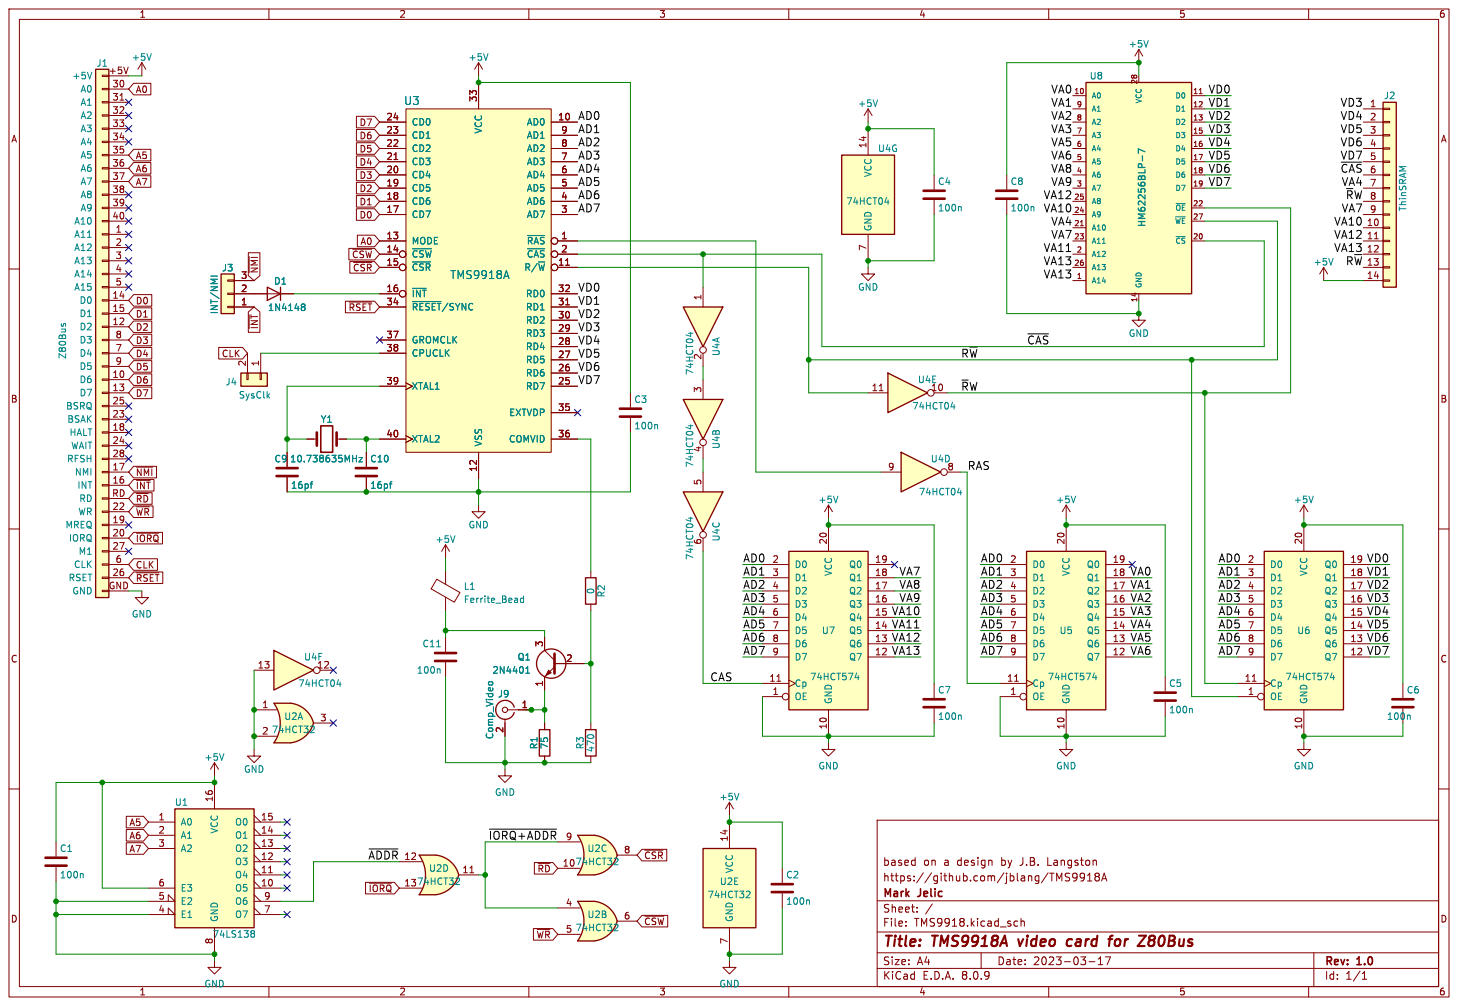
[picture p198: page 1]

https://github.com/jblang/TMS9918A
File: TMS9918.kicad_sch Sheet: / Mark Jelic

Id: 1/1 Title: TMS9918A video card for Z80Bus
