MarkJelic/TEC-1G/Keyboards/Tactile/Z80-Matrix_Tactile-Keyboard_Schematic.pdf

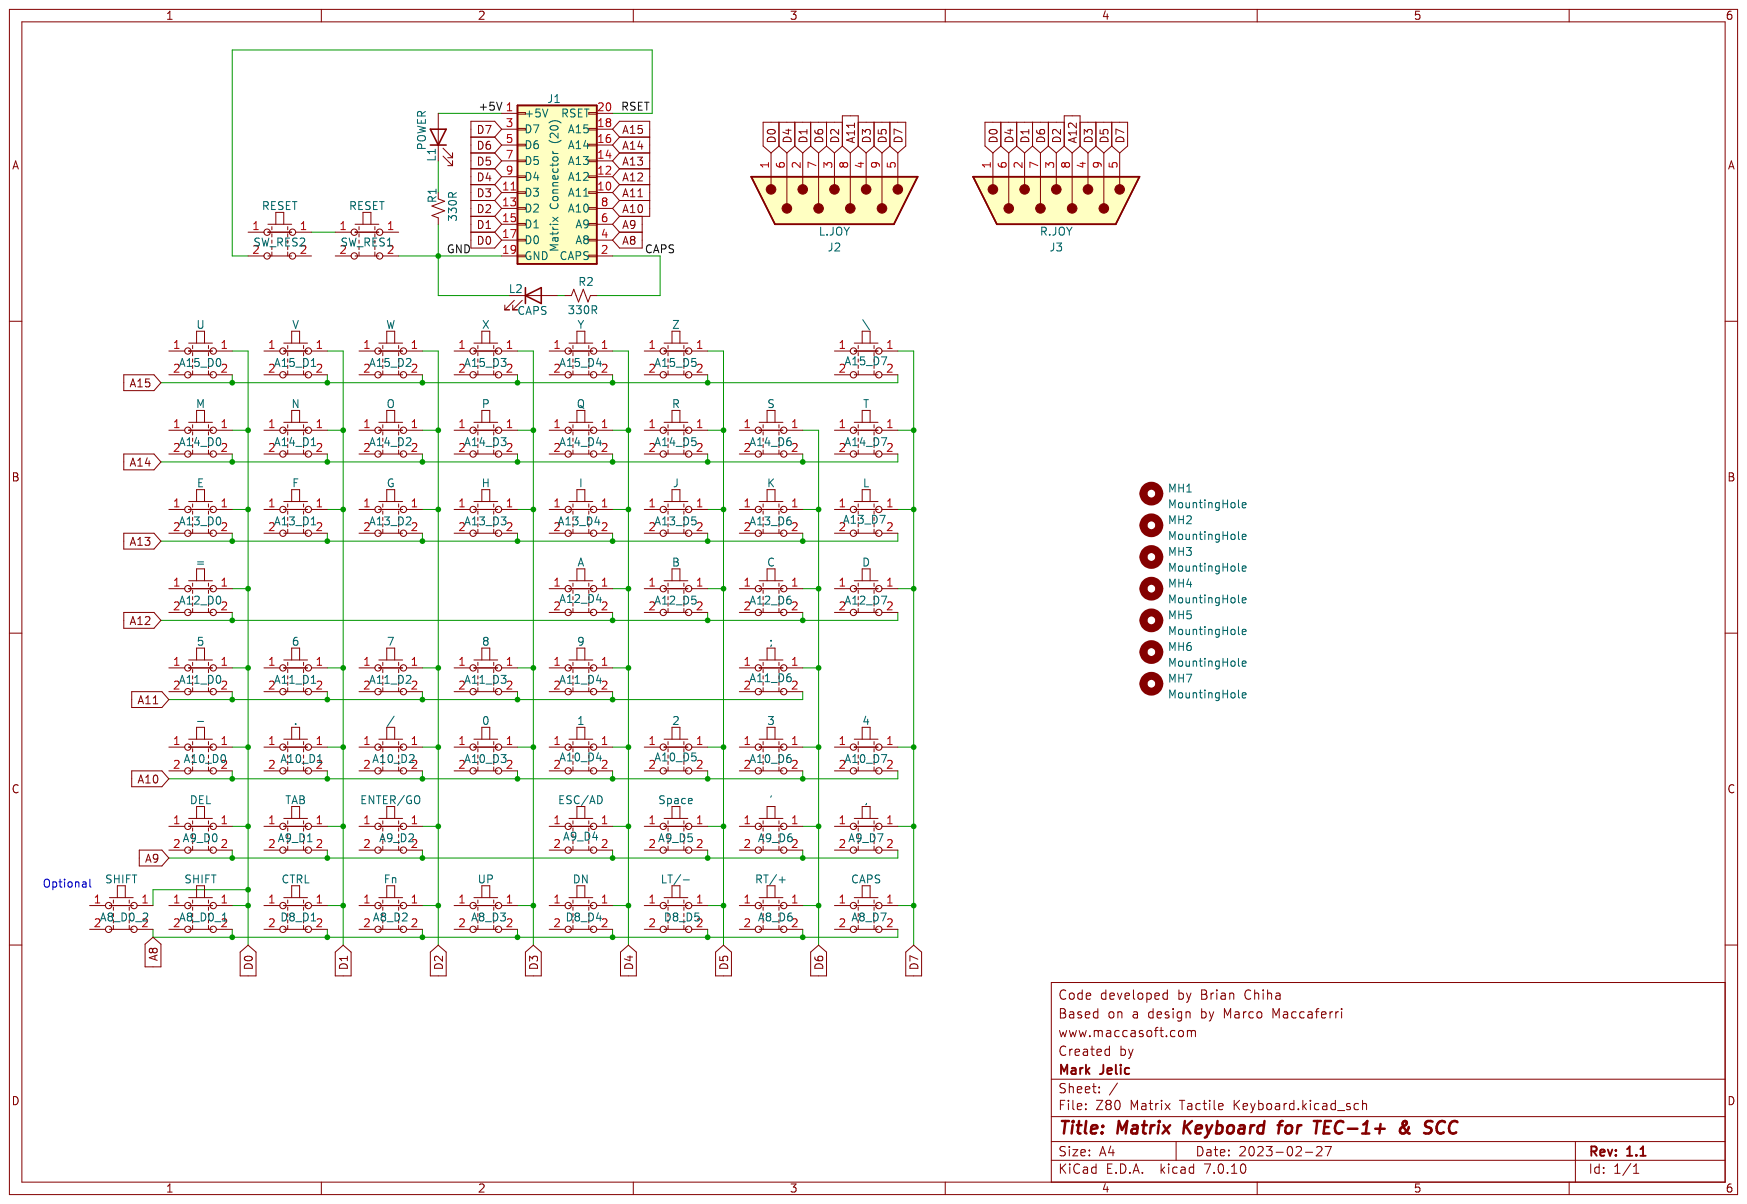
[picture p203: page 1]
