MarkJelic/TEC-1G/GPIO/Printer/TEC-1G_GPIO_Printer_Schematic_v1-1.pdf

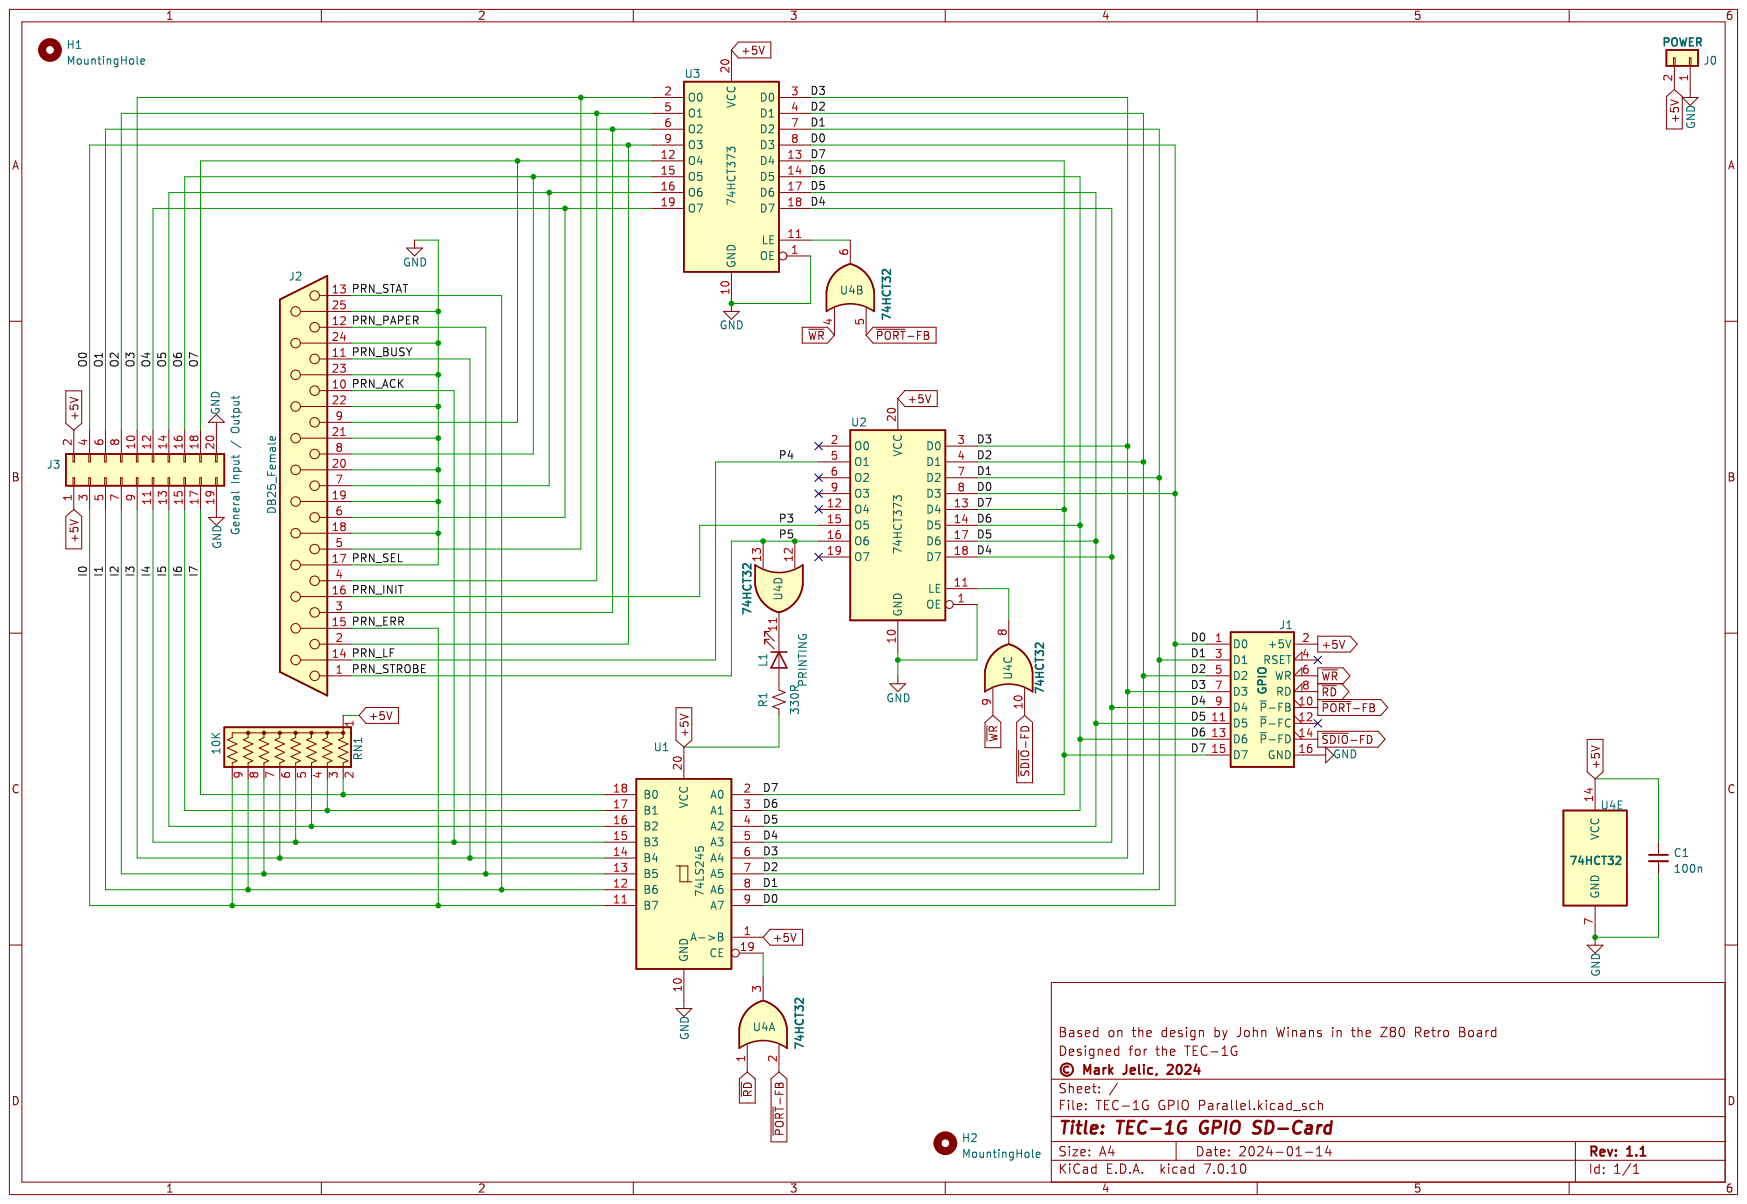
[picture p204: page 1]
