MarkJelic/TEC-1G/GPIO/SD-Card/TEC-1G_GPIO_SD-Card_Schematic_v1-2.pdf

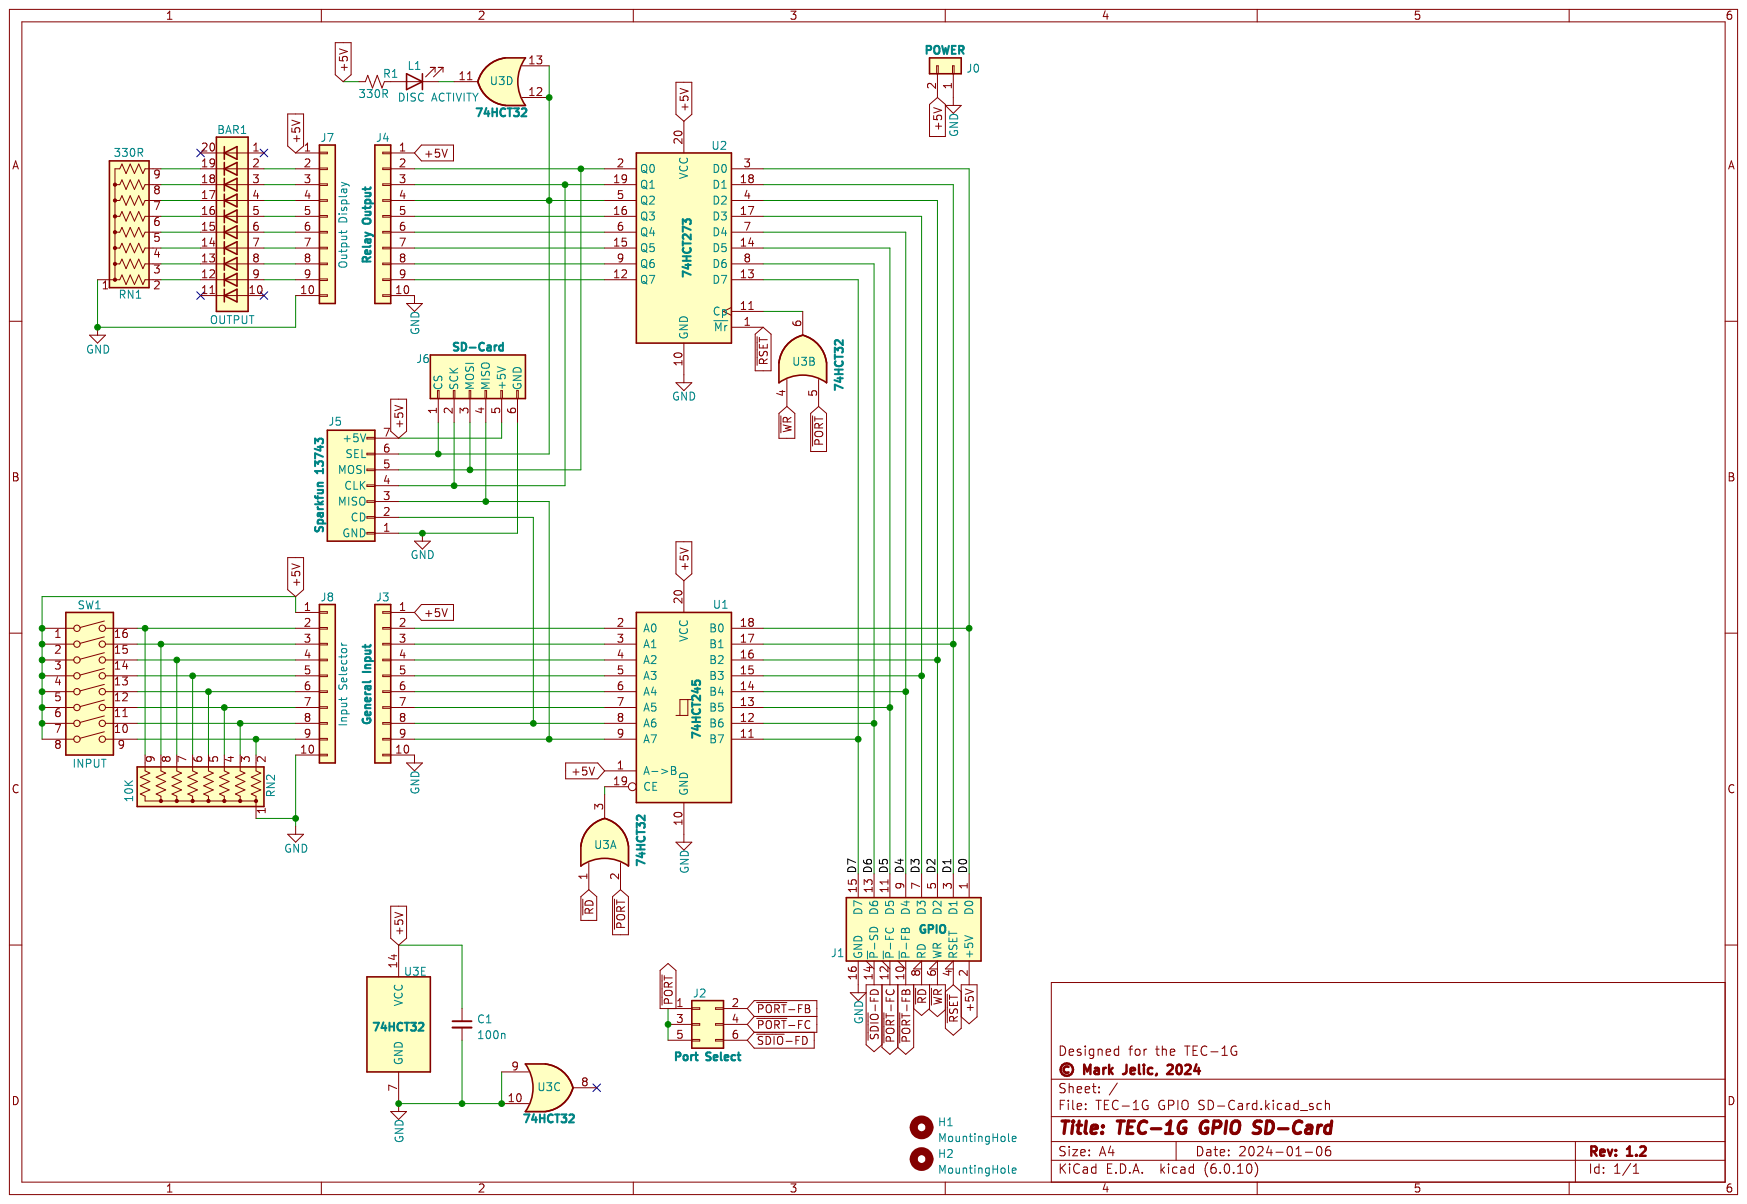
[picture p205: page 1]
