MarkJelic/TEC-1G/GPIO/RTC/TEC-1G_GPIO_RTC_Schematic_v1-0.pdf

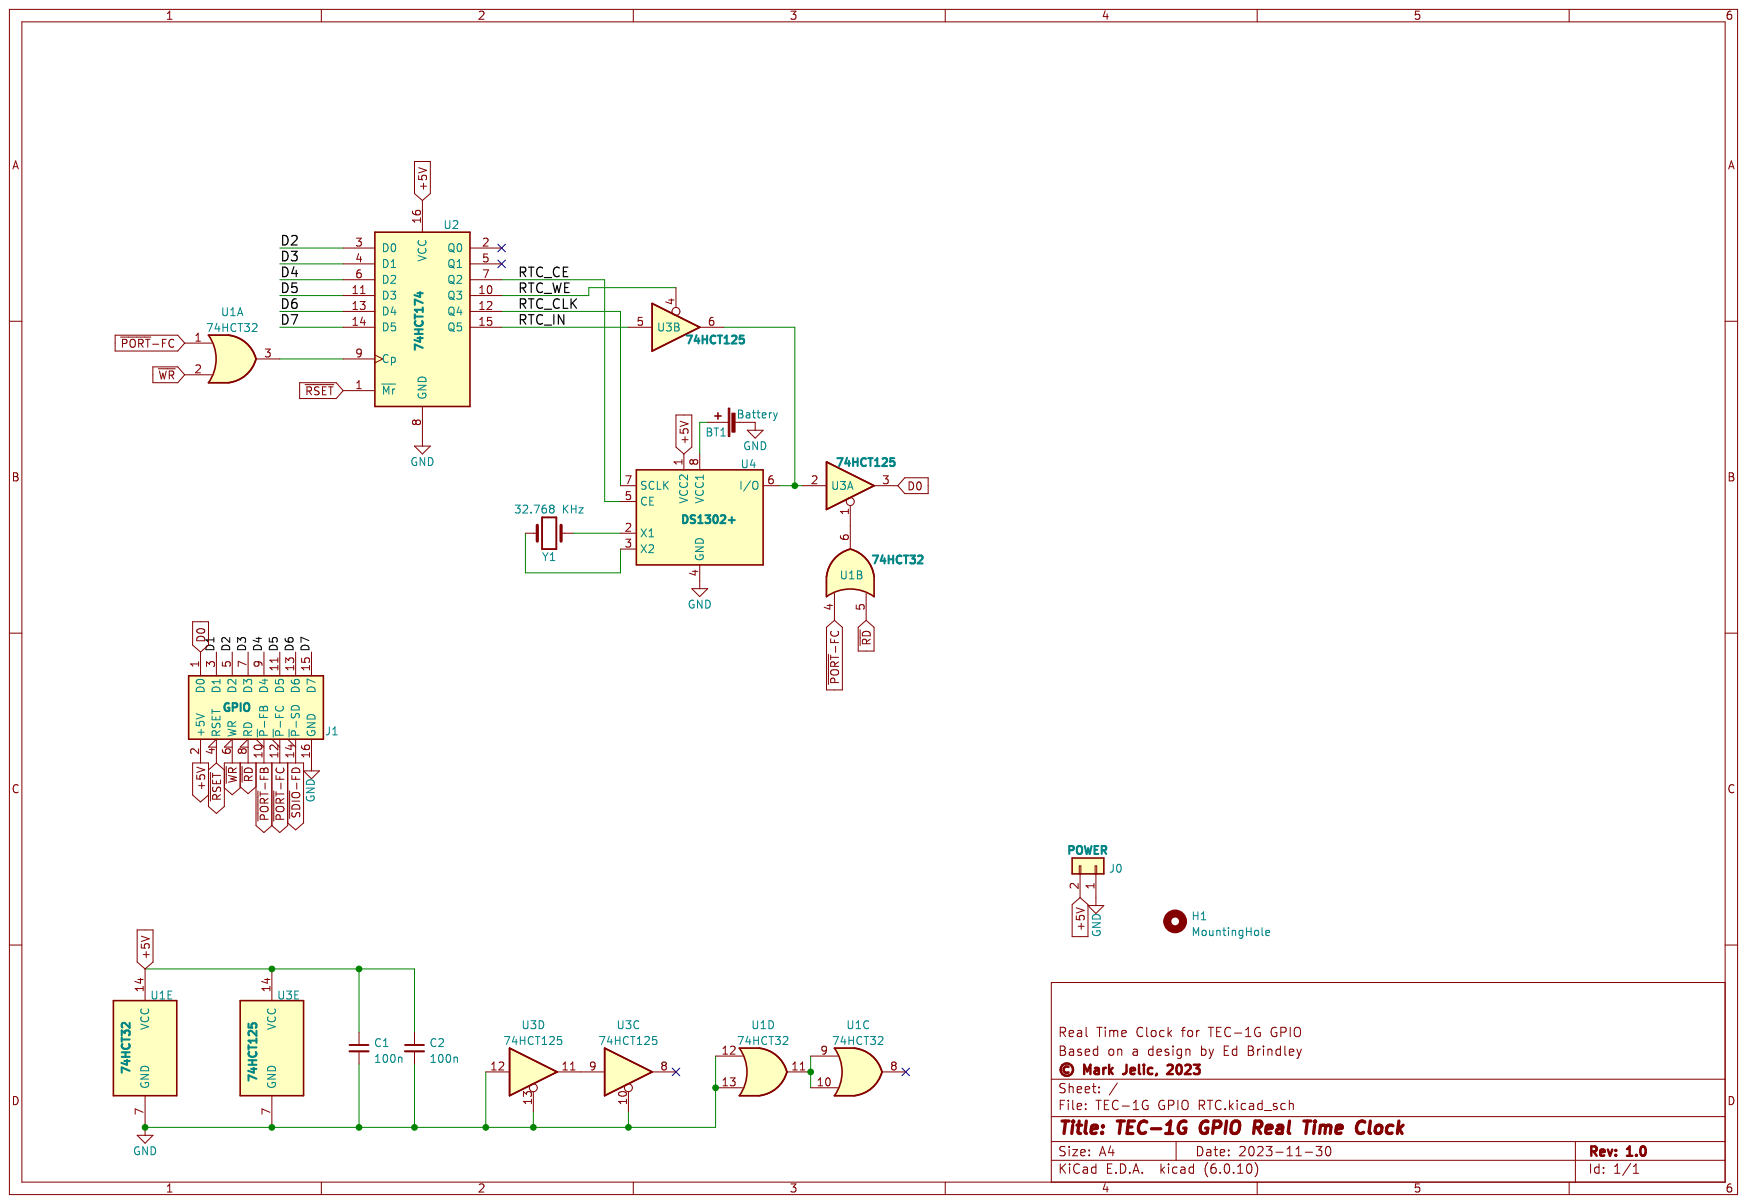
[picture p206: page 1]
