MarkJelic/TEC-1G/Z80Bus/X4/Z80Bus_X4_Schematic.pdf

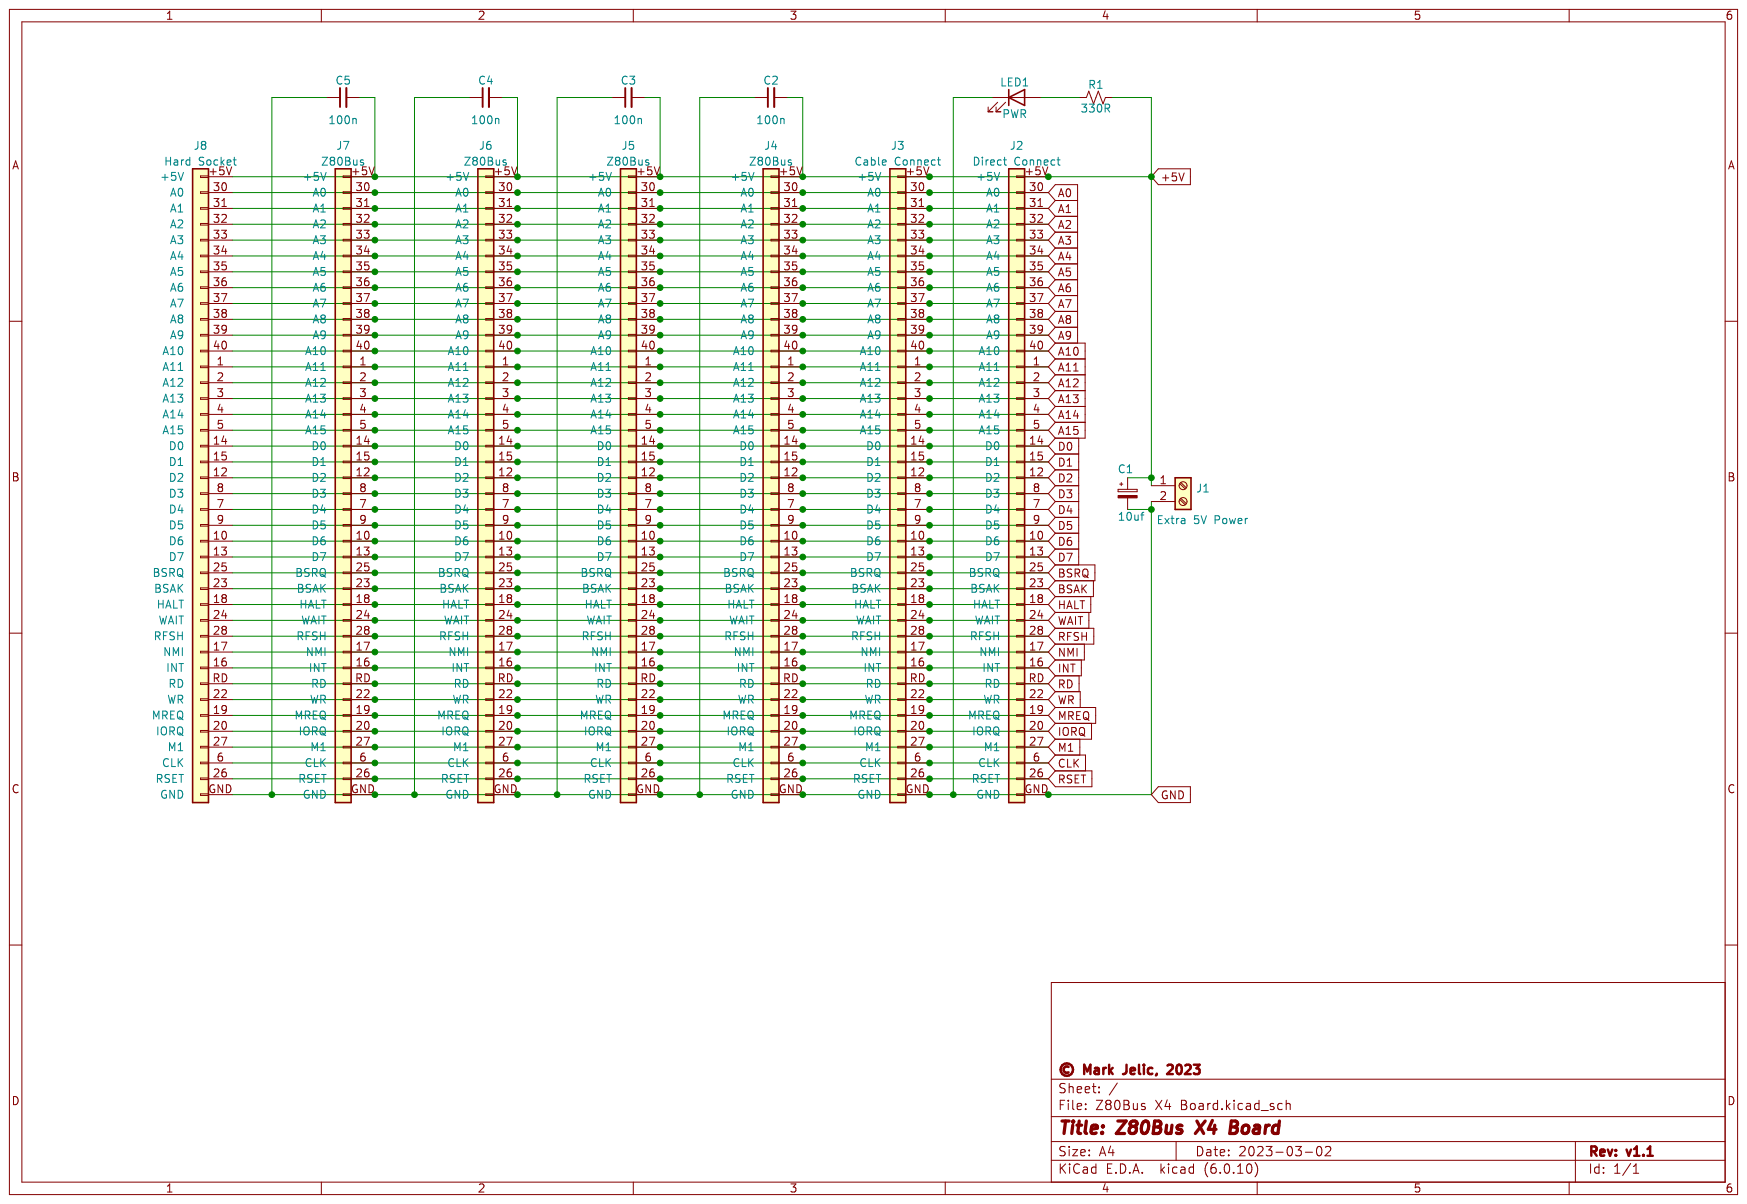
[picture p207: page 1]
