MarkJelic/TEC-1G/TEC-Deck/TMS9918_Video/TEC-Deck_TMS9918_Video_v1-2.pdf

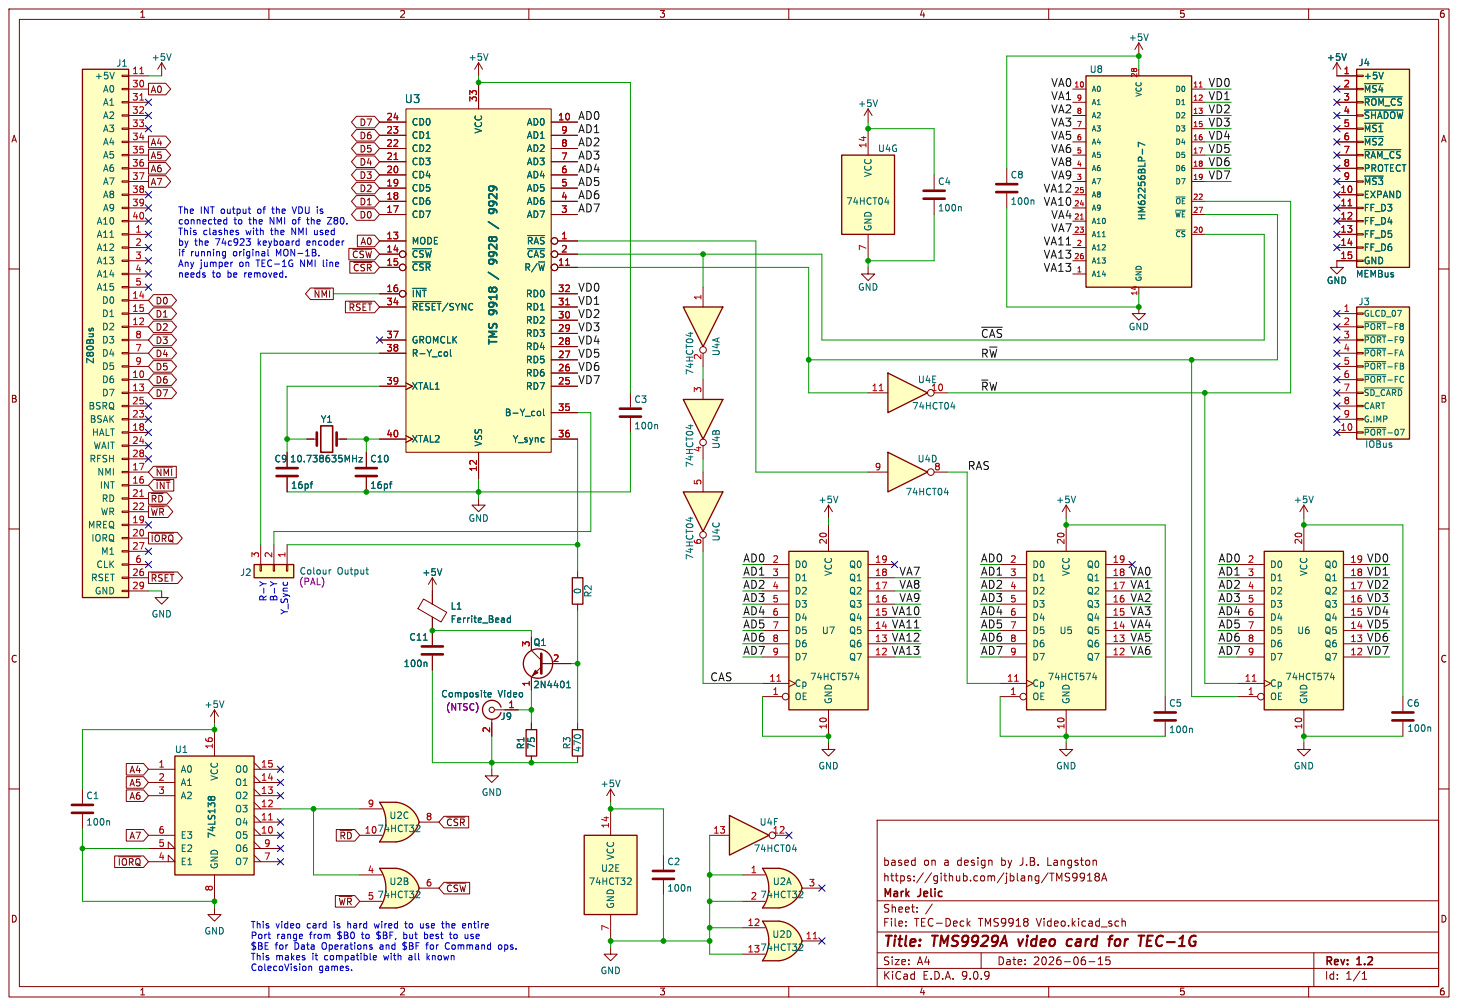
[picture p208: page 1]

3 1 R1 75 U3 TMS 9918 / 9928 / 9929 CD0 24 CD1 23 CD2 22 CD3 21 CD4 20 CD5 19 CD6 18 CD7 17 MODE 13 ~{CSW} 14 ~{CSR} 15 ~{INT} 16 ~{RESET}/SYNC 34 GROMCLK 37 R-Y_col 38 XTAL1 39 XTAL2 40 VCC 33 VSS 12 AD0 10 AD1 9 AD2 8 AD3 7 AD4 6 AD5 5 AD6 4 AD7 3 ~{RAS} 1 ~{CAS} 2 R/~{W} 11 RD0 32 RD1 31 RD2 30 RD3 29 RD4 28 RD5 27 RD6 26 RD7 25 B-Y_col 35 Y_sync 36 C9

The INT output of the VDU is
74HCT32 C9

needs to be removed.

https://github.com/jblang/TMS9918A

Id: 1/1 Title: TMS9929A video card for TEC-1G

This video card is hard wired to use the entire Port range from $B0 to $BF, but best to use
