MarkJelic/TEC-1G/TEC-Deck/TMS9918_Video/TEC-Deck_TMS9918_Video_v1-1.pdf

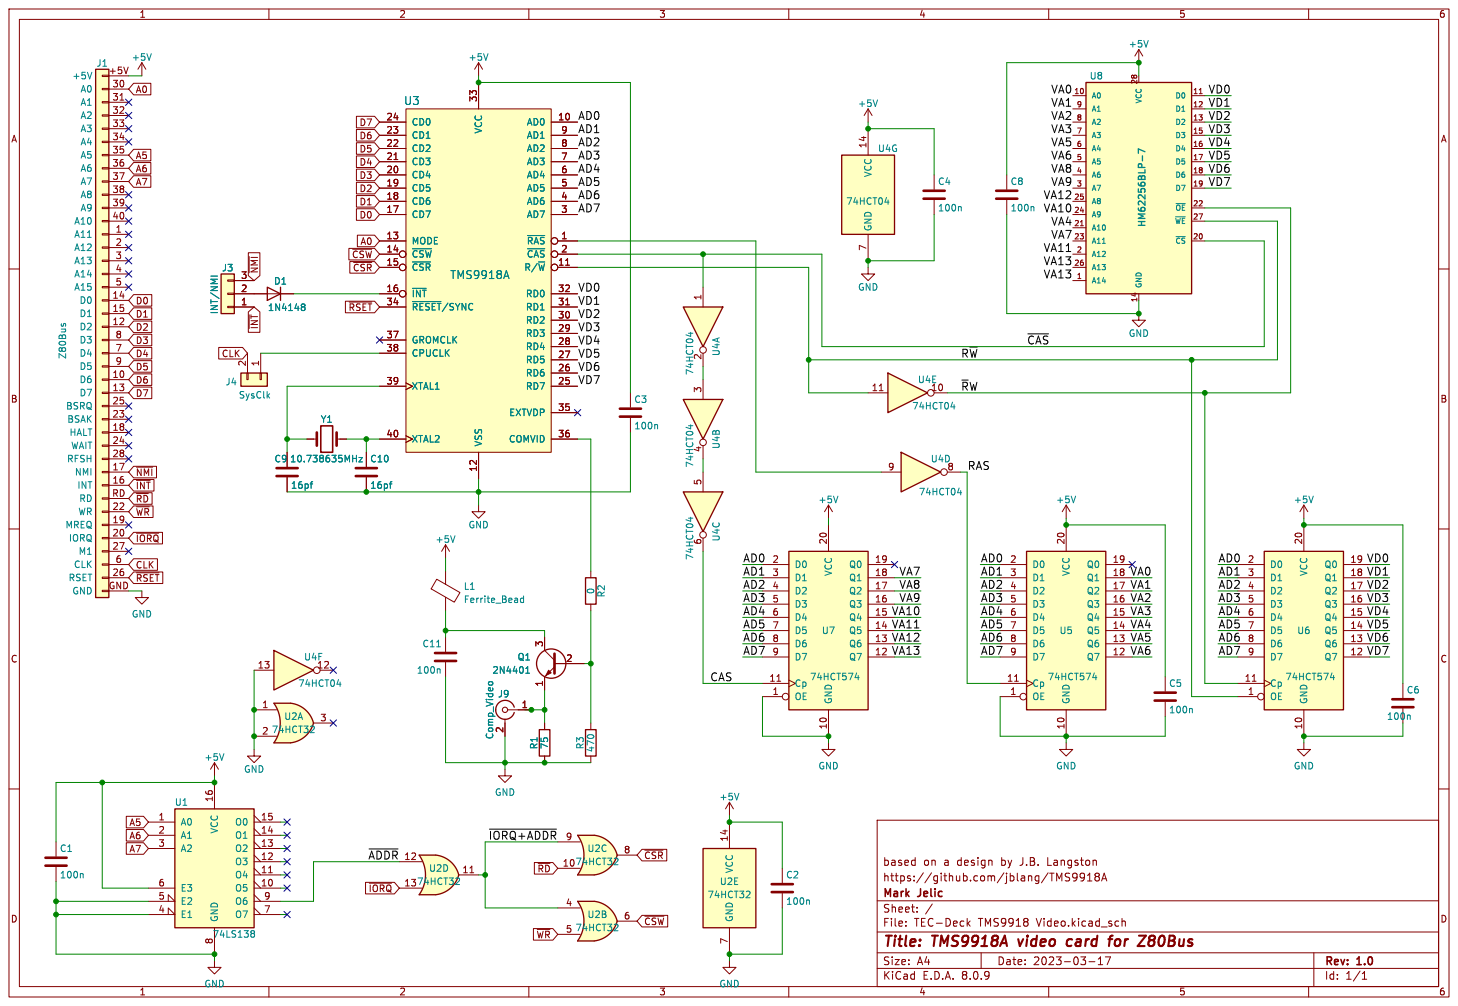
[picture p209: page 1]

https://github.com/jblang/TMS9918A

Id: 1/1 Title: TMS9918A video card for Z80Bus
